oserratr/head-md-caran-ache-project/form/2023-12-11/forme2.pdf

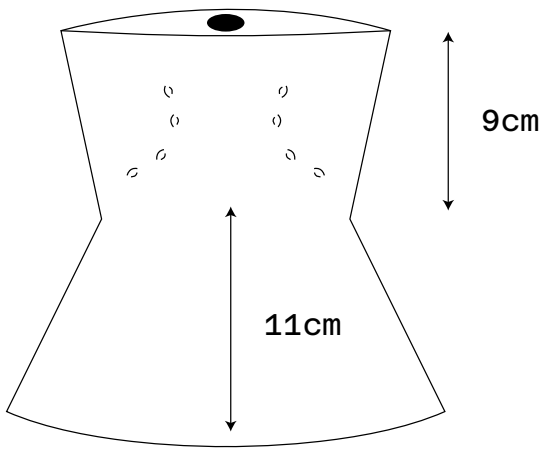
[picture p66: figure]
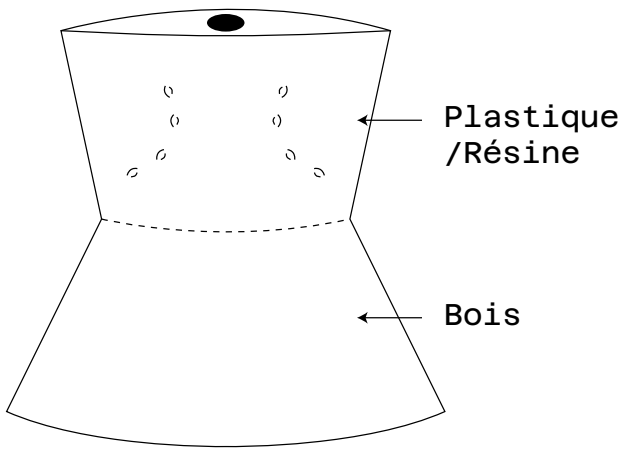
[picture p67: figure]
Bois; Plastique /Résine

20cm

Dimensions, matériaux, forme objet 2, prise a 2 mains

De côté

De dessus | 6cm

2cm

Bois peint
