oserratr/head-md-caran-ache-project/process/2023-11-13/part1-proto-final.pdf

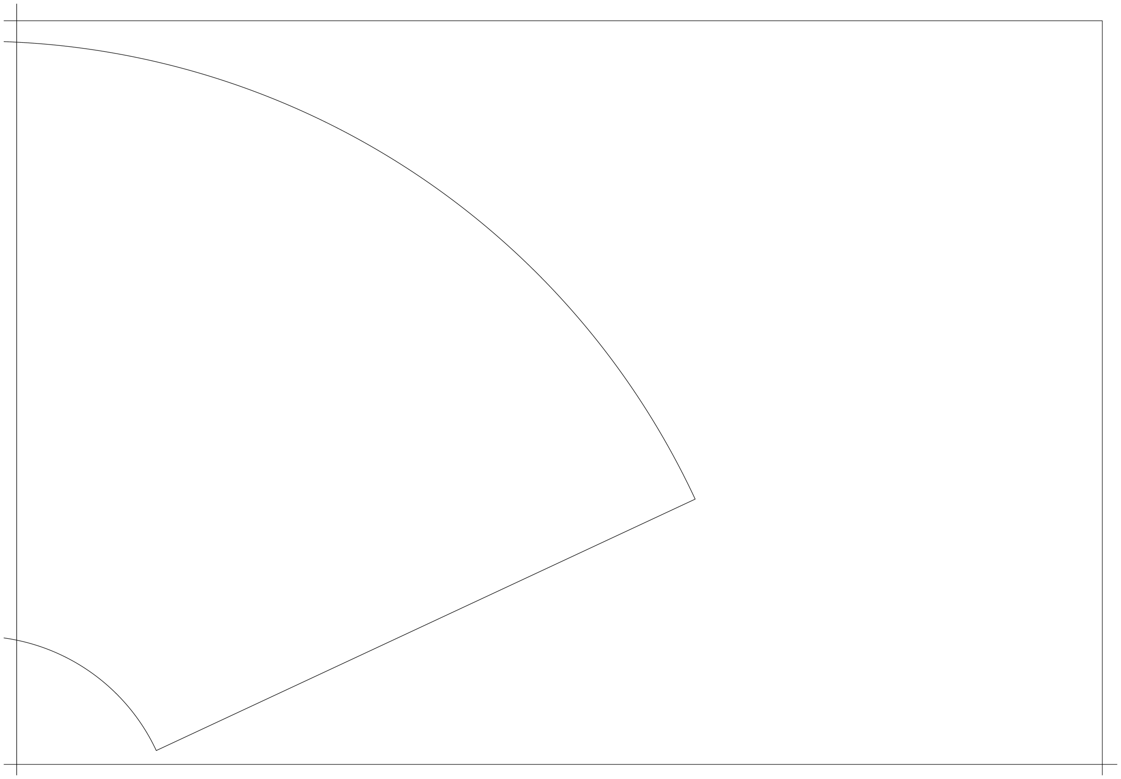
[picture p89: page 1]
