oserratr/head-md-caran-ache-project/process/2023-11-13/part2-proto-final.pdf

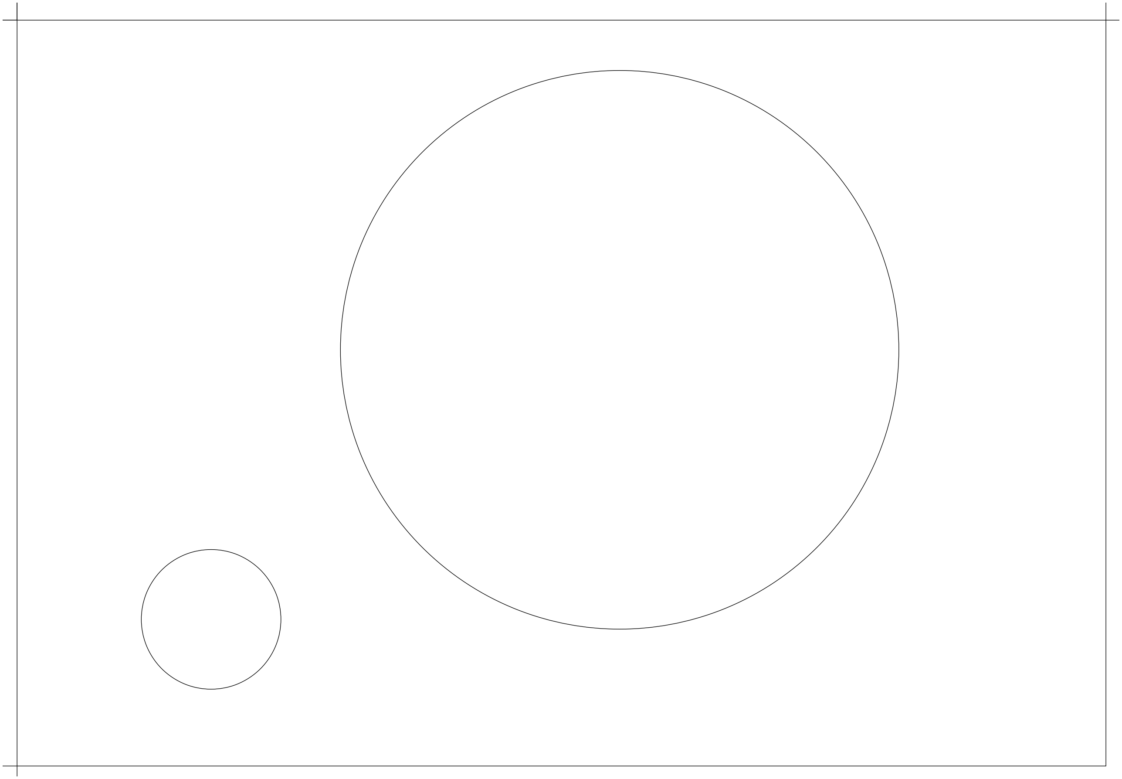
[picture p90: figure]
