oserratr/head-md-caran-ache-project/process/2023-11-13/part3-proto-final.pdf

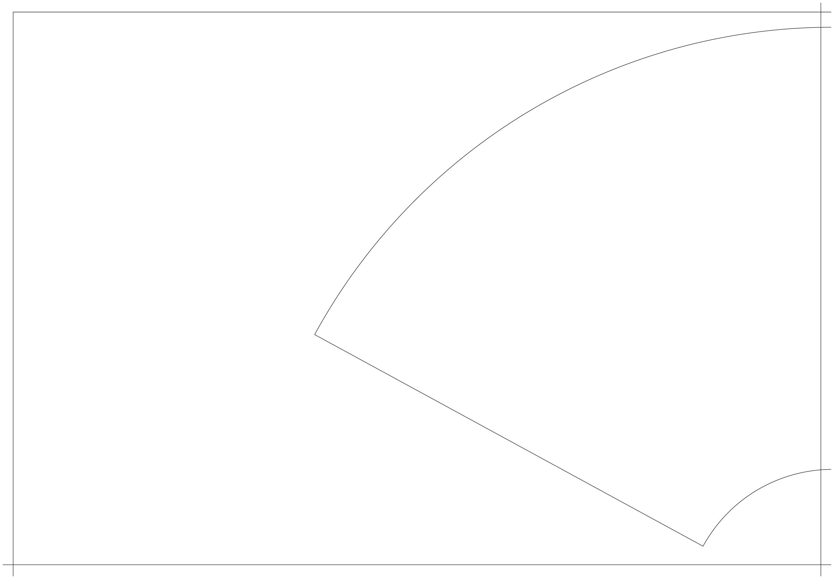
[picture p91: page 1]
