oserratr/head-md-caran-ache-project/process/2023-11-13/impression proto 2.pdf

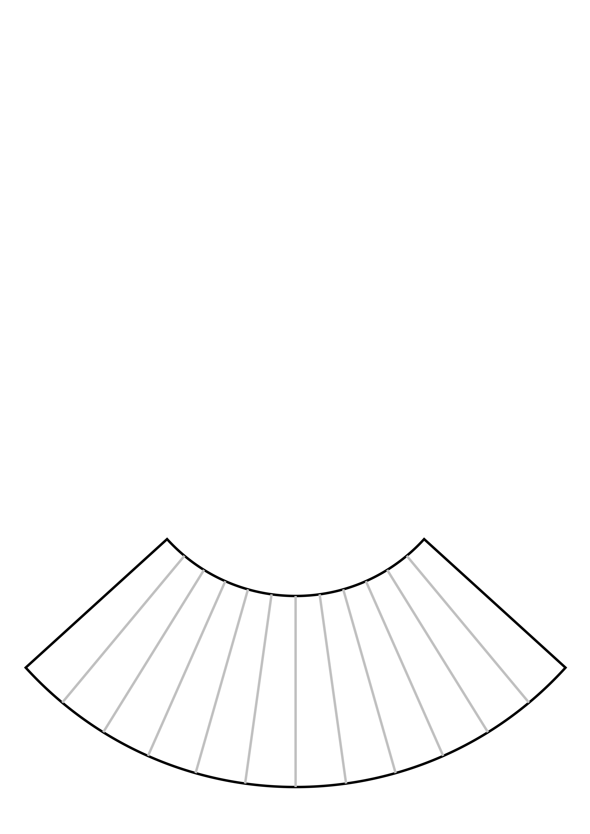
[picture p92: page 1]
