oserratr/head-md-caran-ache-project/process/2023-11-13/impression proto.pdf

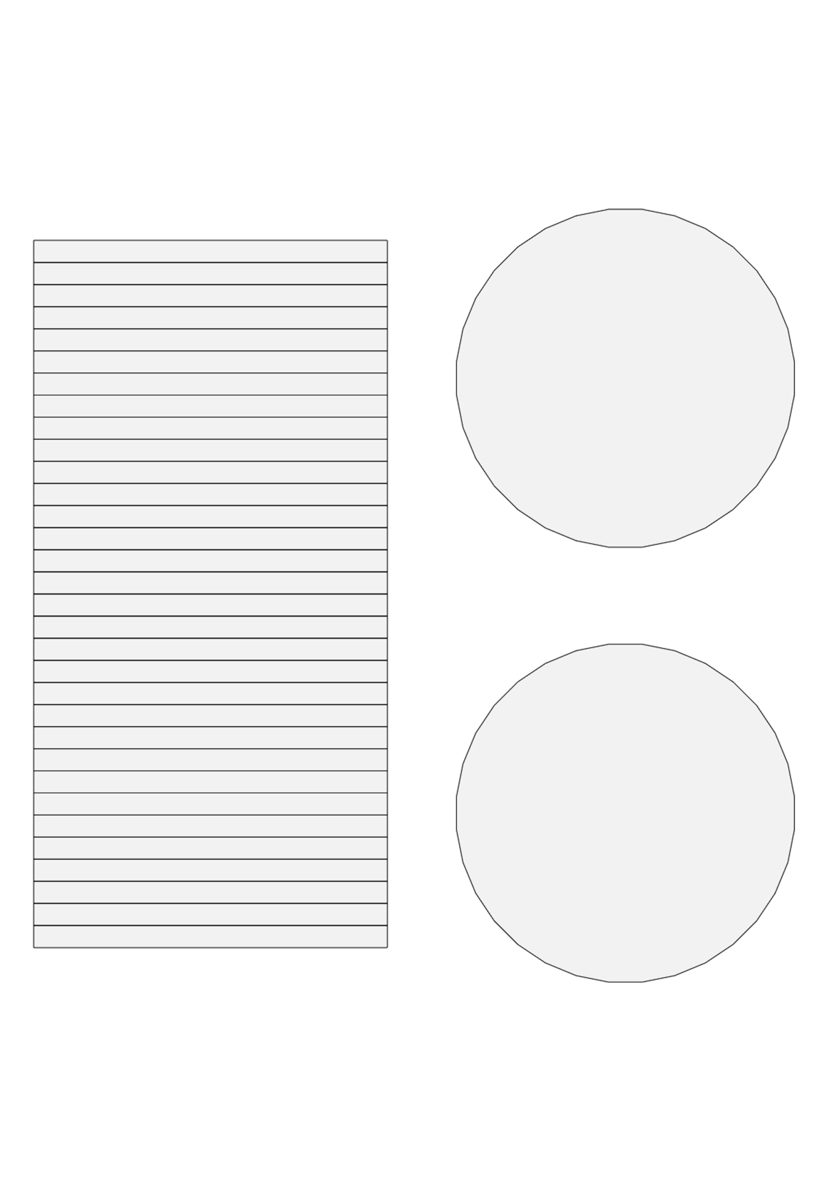
[picture p93: page 1]
