oserratr/head-md-caran-ache-project/electronics/2023-12-11/essais.png

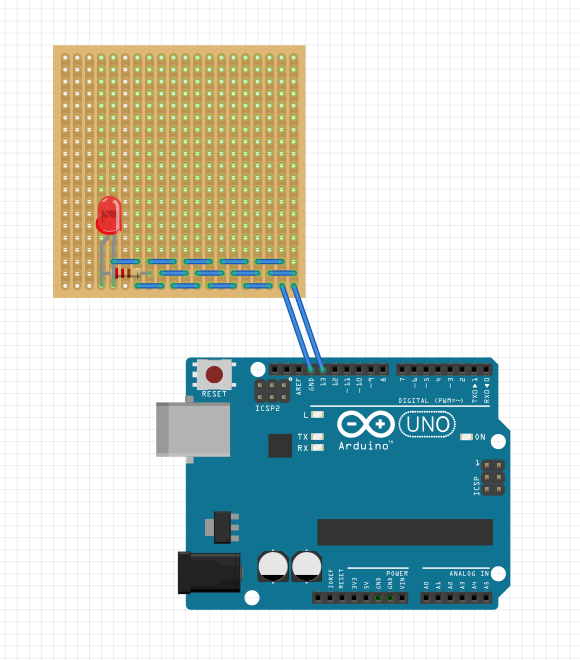
electronics/2023-12-11/essais.png
