oserratr/head-md-caran-ache-project/electronics/2023-12-11/shema.png

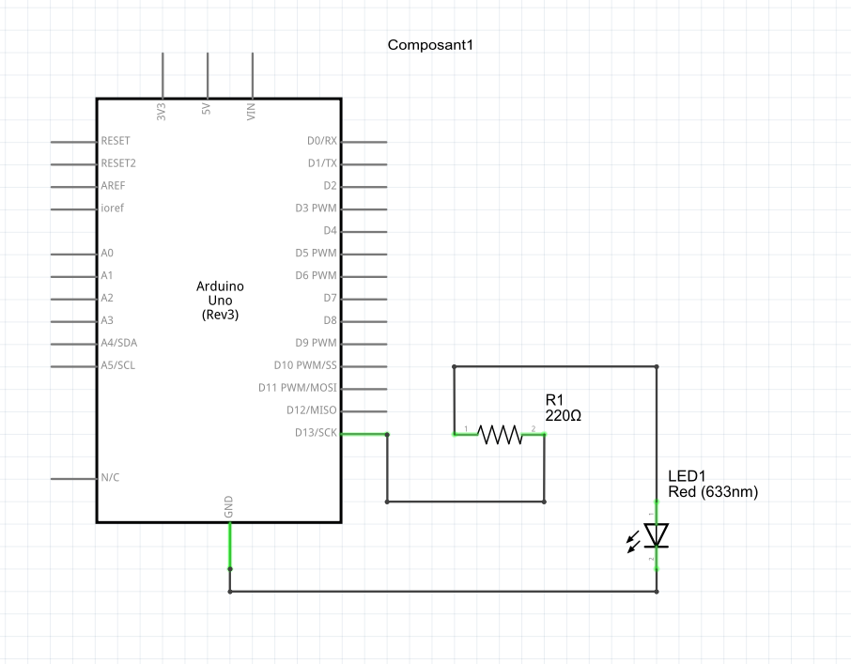
electronics/2023-12-11/shema.png
