oserratr/head-md-caran-ache-project/electronics/2023-12-21/connexion-bt-esp32-2.png

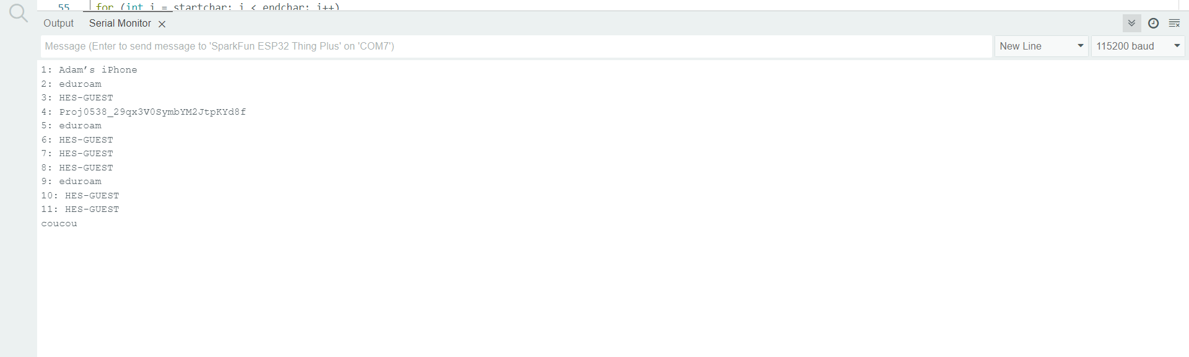
electronics/2023-12-21/connexion-bt-esp32-2.png
