oserratr/head-md-caran-ache-project/electronics/2024-01-14/landscape_design/output.png

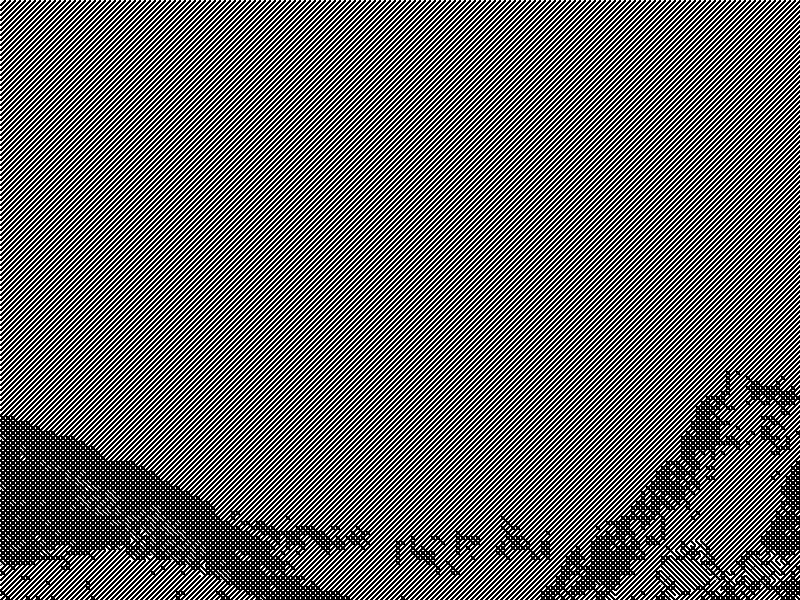
electronics/2024-01-14/landscape_design/output.png
