oserratr/head-md-caran-ache-project/form/2023-12-12/atelier1.jpg

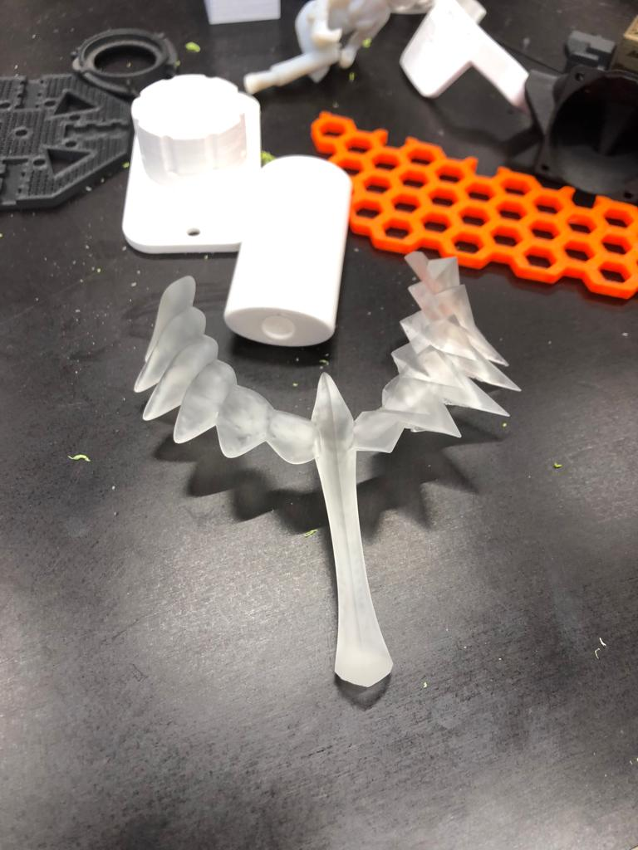
form/2023-12-12/atelier1.jpg
