oserratr/head-md-caran-ache-project/form/2023-12-12/dimensions-base-objet-bois.png

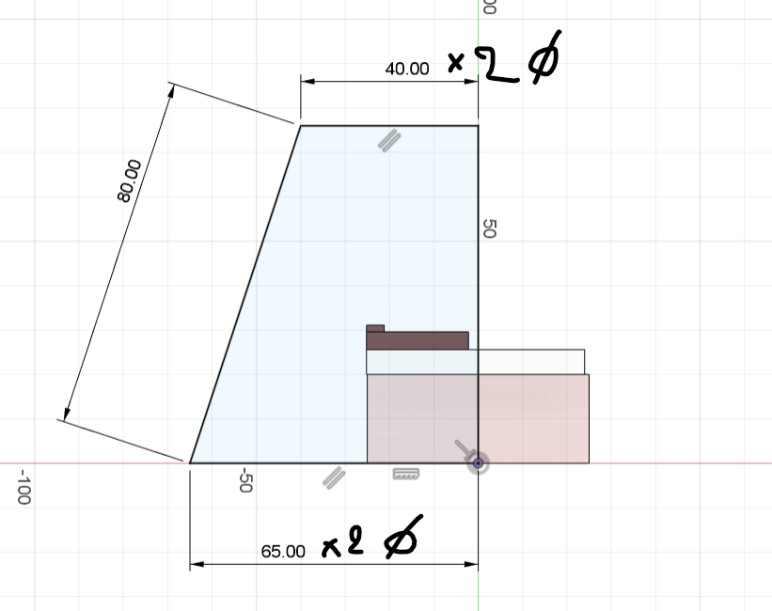
form/2023-12-12/dimensions-base-objet-bois.png
