oserratr/head-md-caran-ache-project/form/2023-12-12/dimensions-fixer-forme2.png

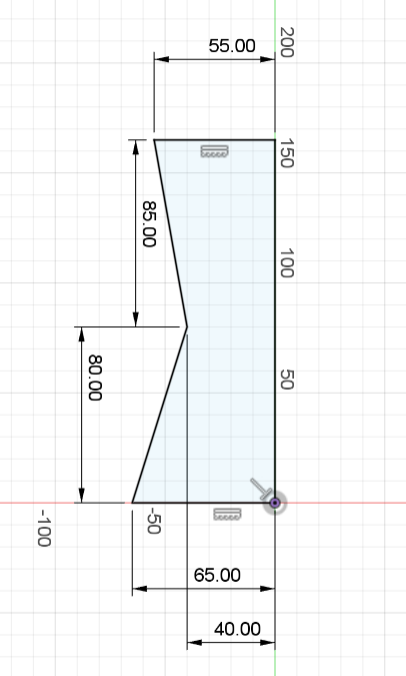
form/2023-12-12/dimensions-fixer-forme2.png
