oserratr/head-md-caran-ache-project/form/2023-12-12/taille-composants-inside.png

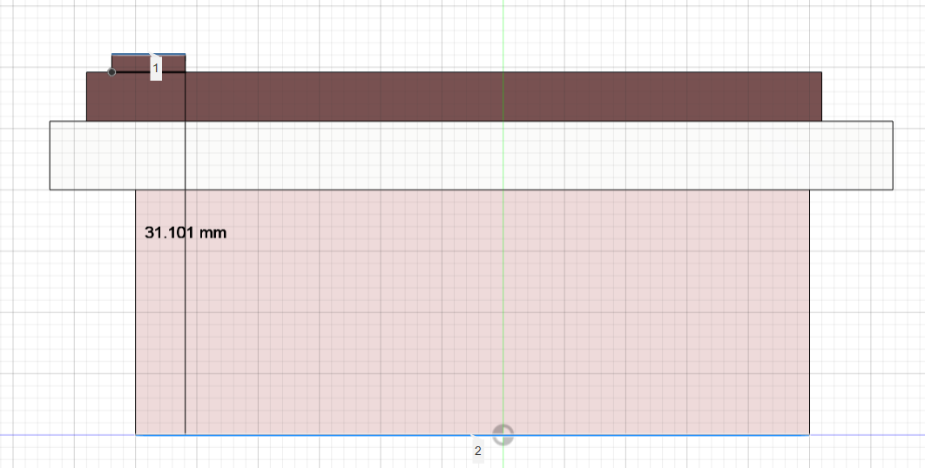
form/2023-12-12/taille-composants-inside.png
