oserratr/head-md-caran-ache-project/form/2023-12-19/manche.png

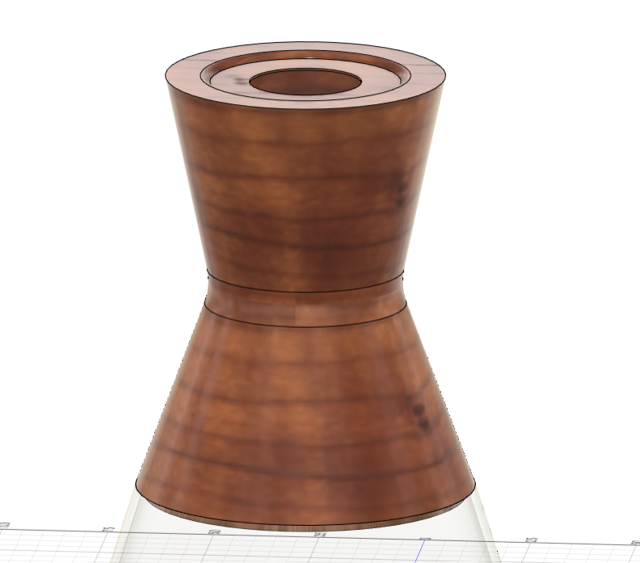
form/2023-12-19/manche.png
