oserratr/head-md-caran-ache-project/form/2023-12-19/socle.png

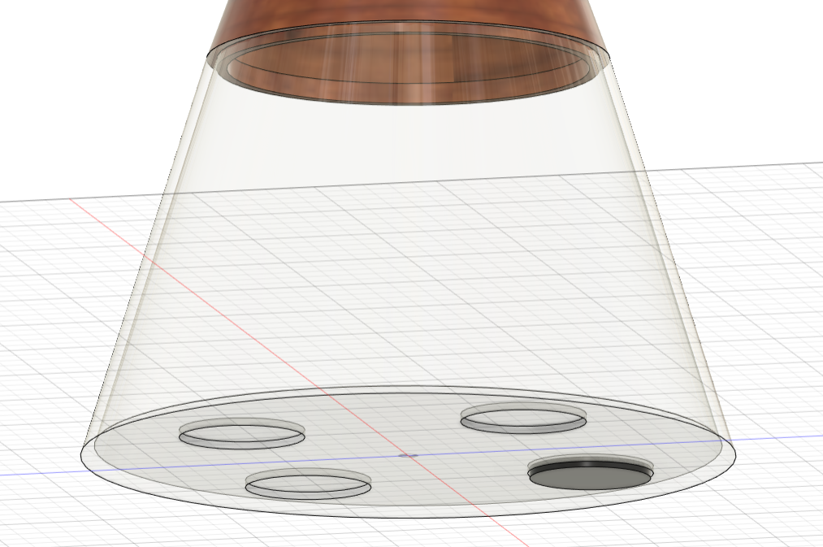
form/2023-12-19/socle.png
