oserratr/head-md-caran-ache-project/form/2023-12-20/impression manche.jpg

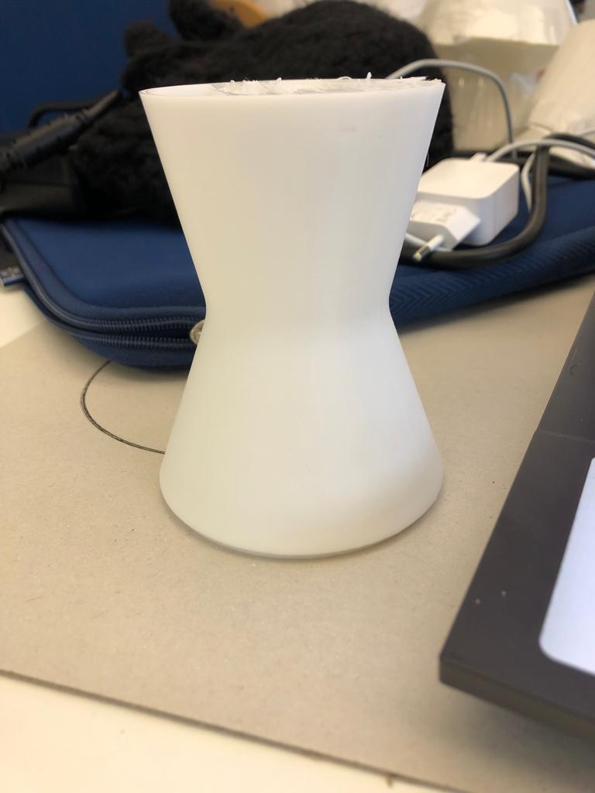
form/2023-12-20/impression manche.jpg
