oserratr/head-md-caran-ache-project/form/2023-12-20/materiel 3D2.jpg

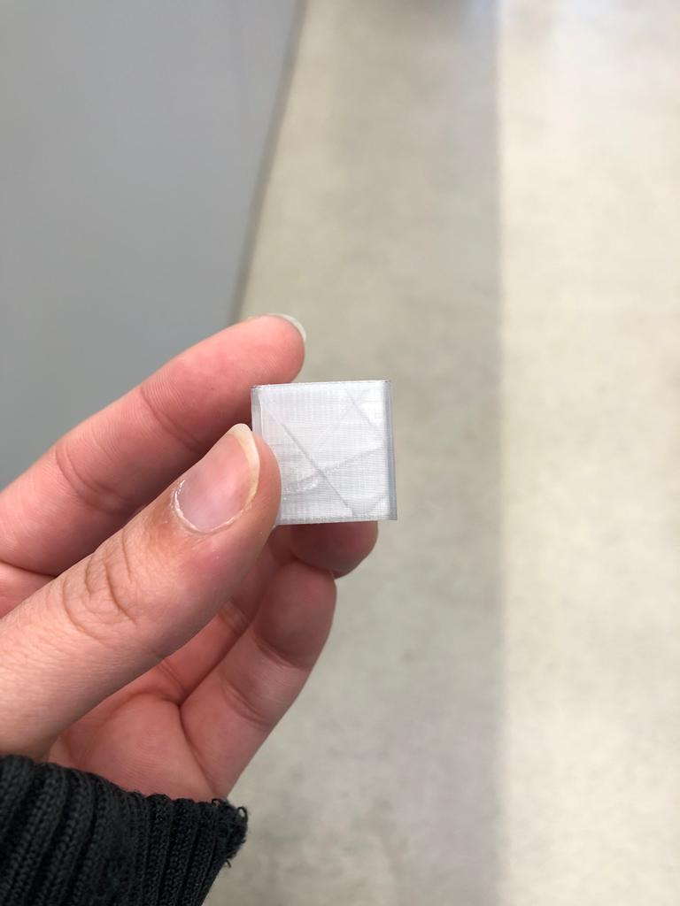
form/2023-12-20/materiel 3D2.jpg
