oserratr/head-md-caran-ache-project/form/2024-01-10/plan-drawing-input.jpg

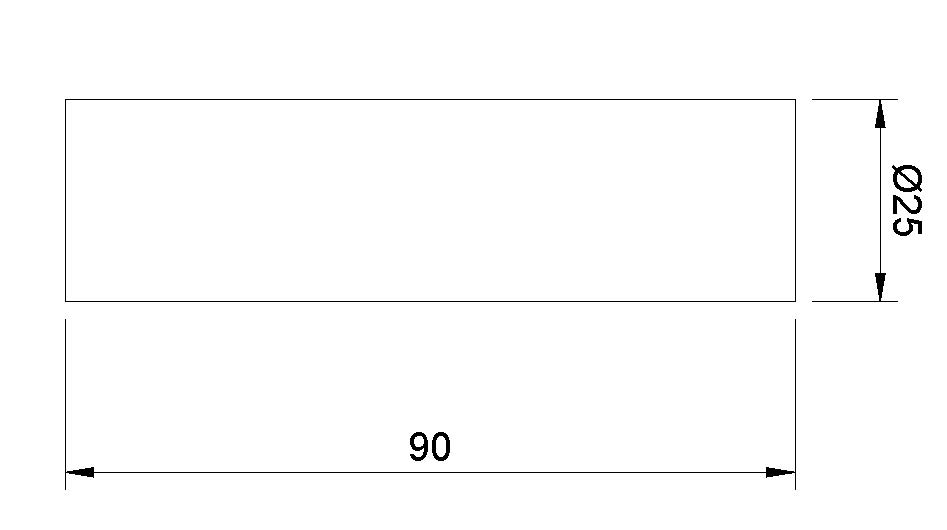
form/2024-01-10/plan-drawing-input.jpg
