oserratr/head-md-caran-ache-project/form/2024-01-10/plan-drawing-perspective.jpg

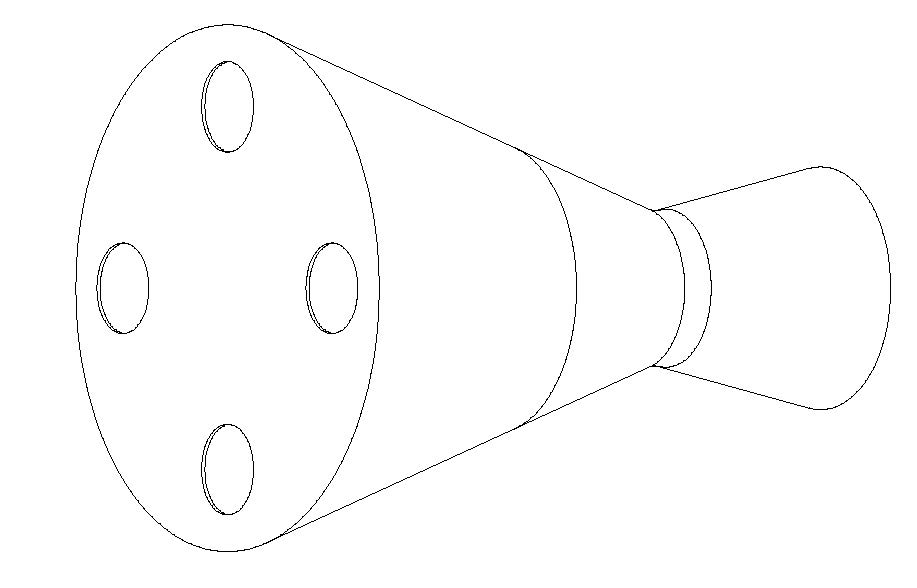
form/2024-01-10/plan-drawing-perspective.jpg
