oserratr/head-md-caran-ache-project/form/2024-01-10/plan-drawing-plateau-2.jpg

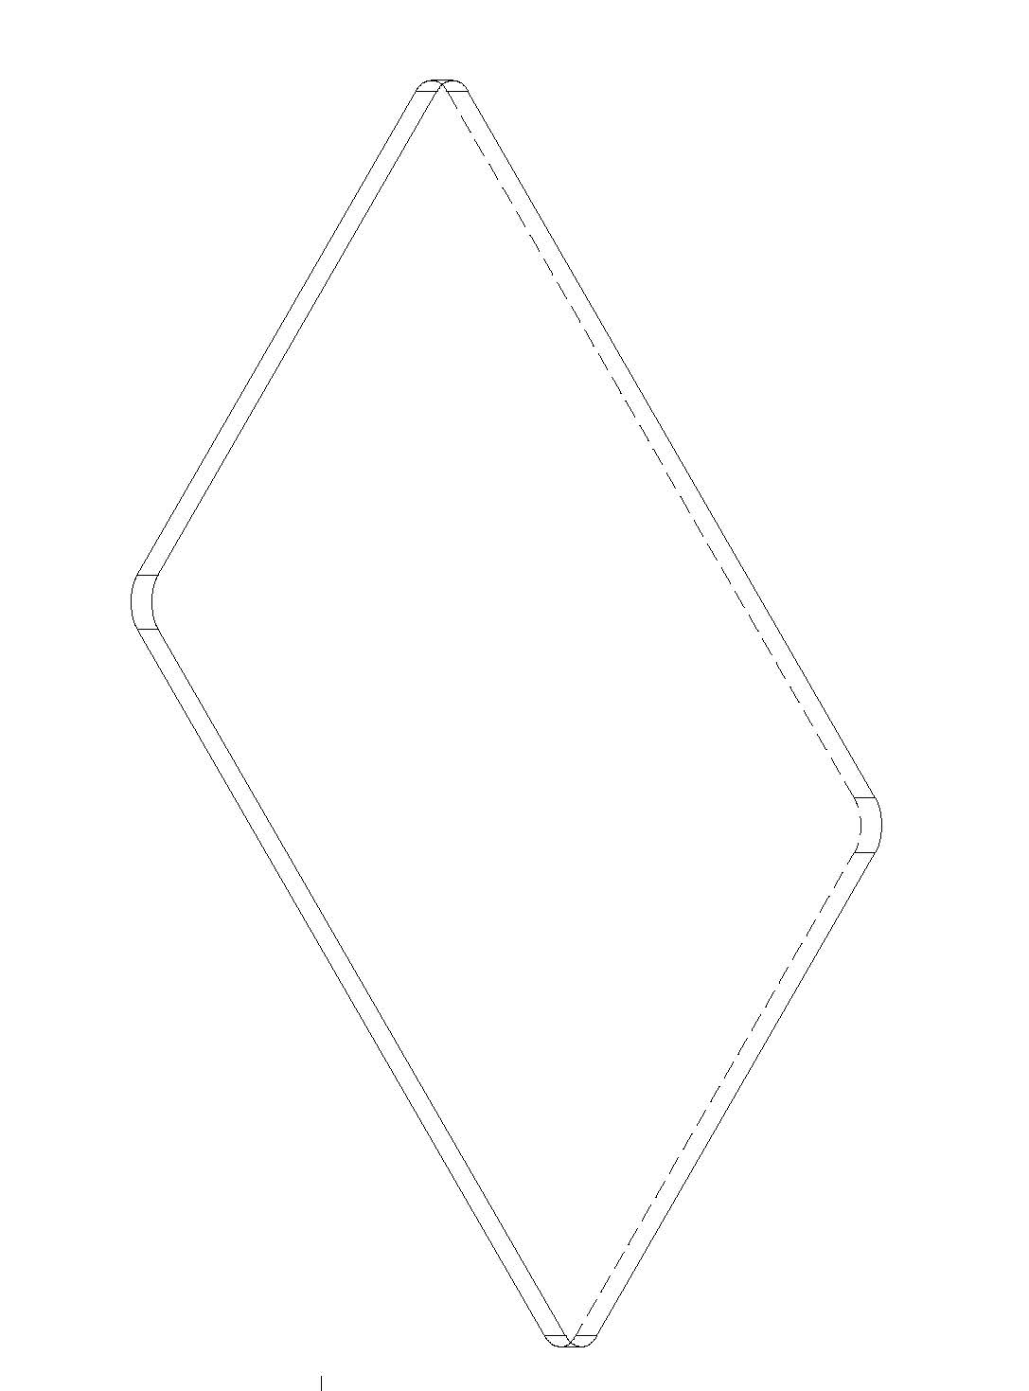
form/2024-01-10/plan-drawing-plateau-2.jpg
