oserratr/head-md-caran-ache-project/form/2024-01-10/plan-drawing-top.jpg

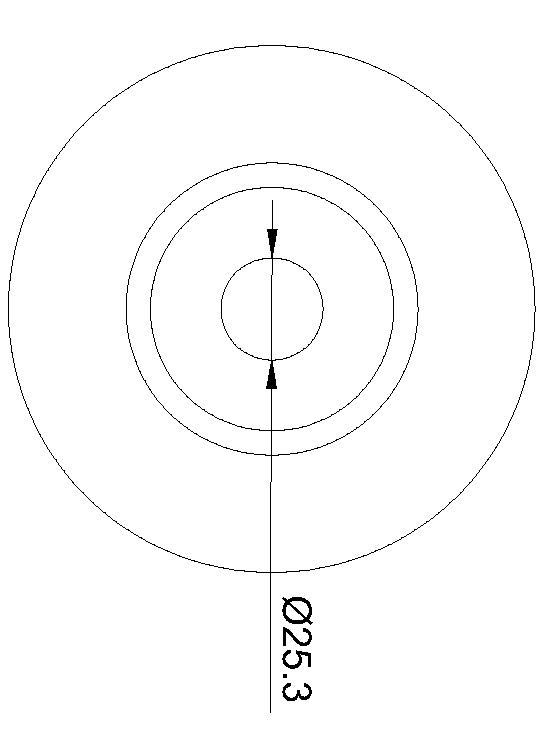
form/2024-01-10/plan-drawing-top.jpg
