oserratr/head-md-caran-ache-project/form/2024-01-11/rendu/rendu1-post.jpg

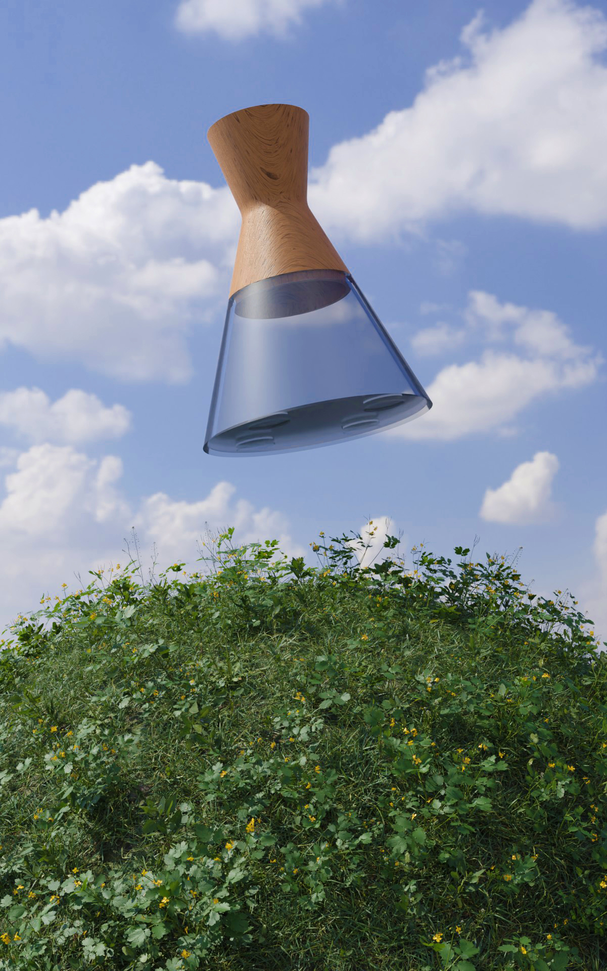
form/2024-01-11/rendu/rendu1-post.jpg
