oserratr/head-md-caran-ache-project/process/2023-10-25/proto-papier-cartes-1.jpeg

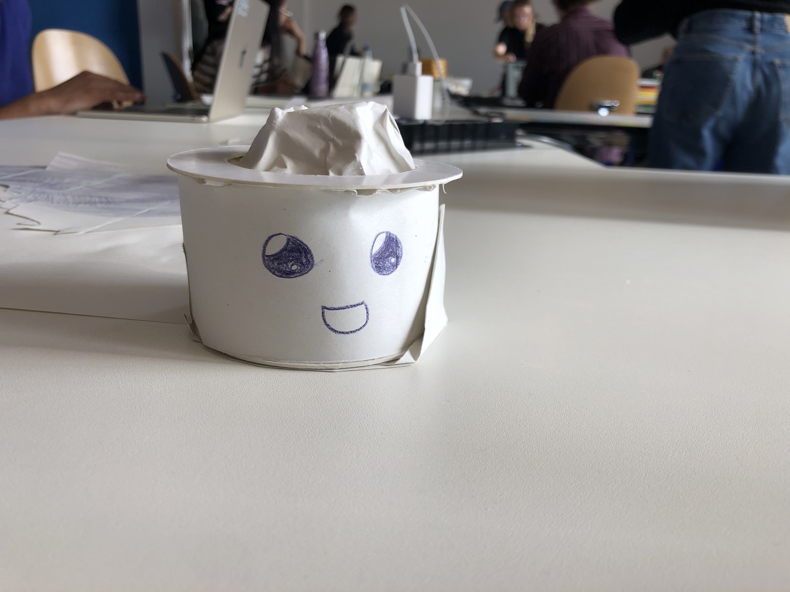
process/2023-10-25/proto-papier-cartes-1.jpeg
