oserratr/head-md-caran-ache-project/process/2023-10-25/proto-papier-cartes.jpeg

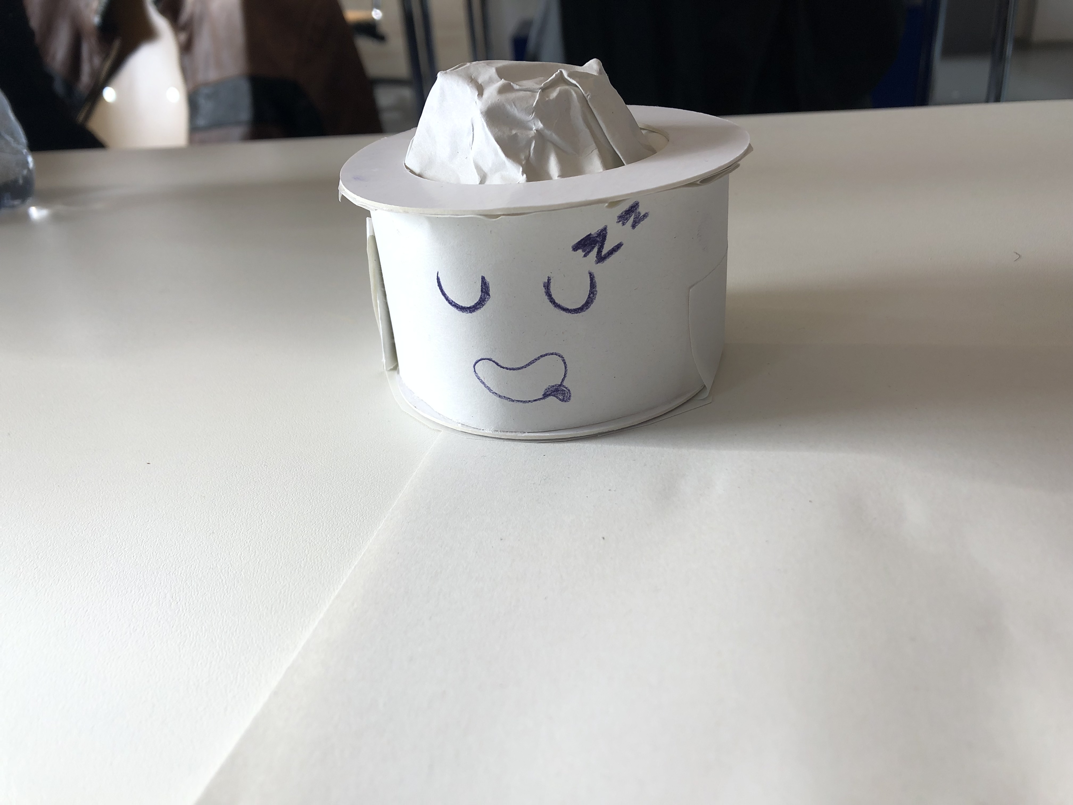
process/2023-10-25/proto-papier-cartes.jpeg
