oserratr/head-md-caran-ache-project/process/2023-10-25/schema-proto.jpg

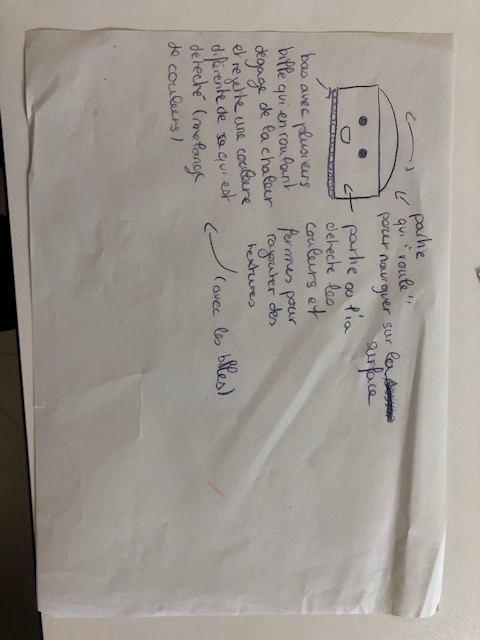
process/2023-10-25/schema-proto.jpg
