oserratr/head-md-caran-ache-project/process/2023-10-30/cote2.jpg

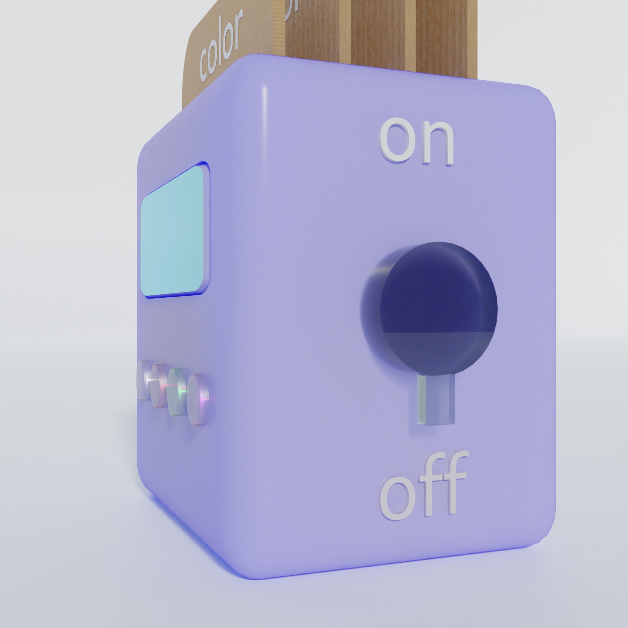
process/2023-10-30/cote2.jpg
