oserratr/head-md-caran-ache-project/process/2023-10-30/face.jpg

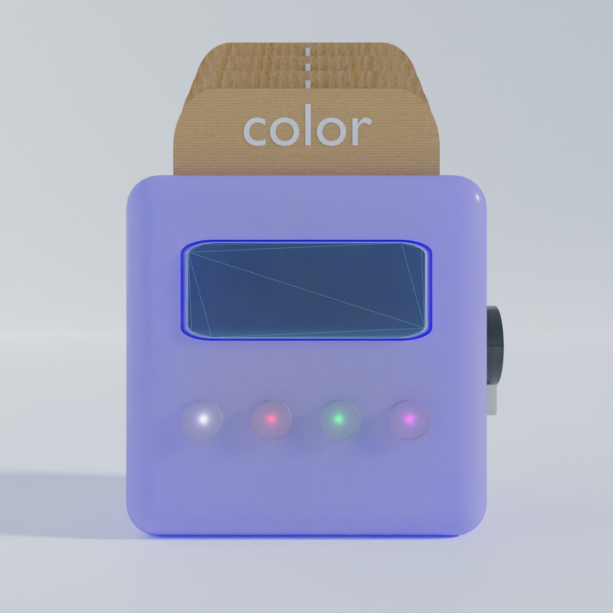
process/2023-10-30/face.jpg
