oserratr/head-md-caran-ache-project/process/2023-10-30/haut2.jpg

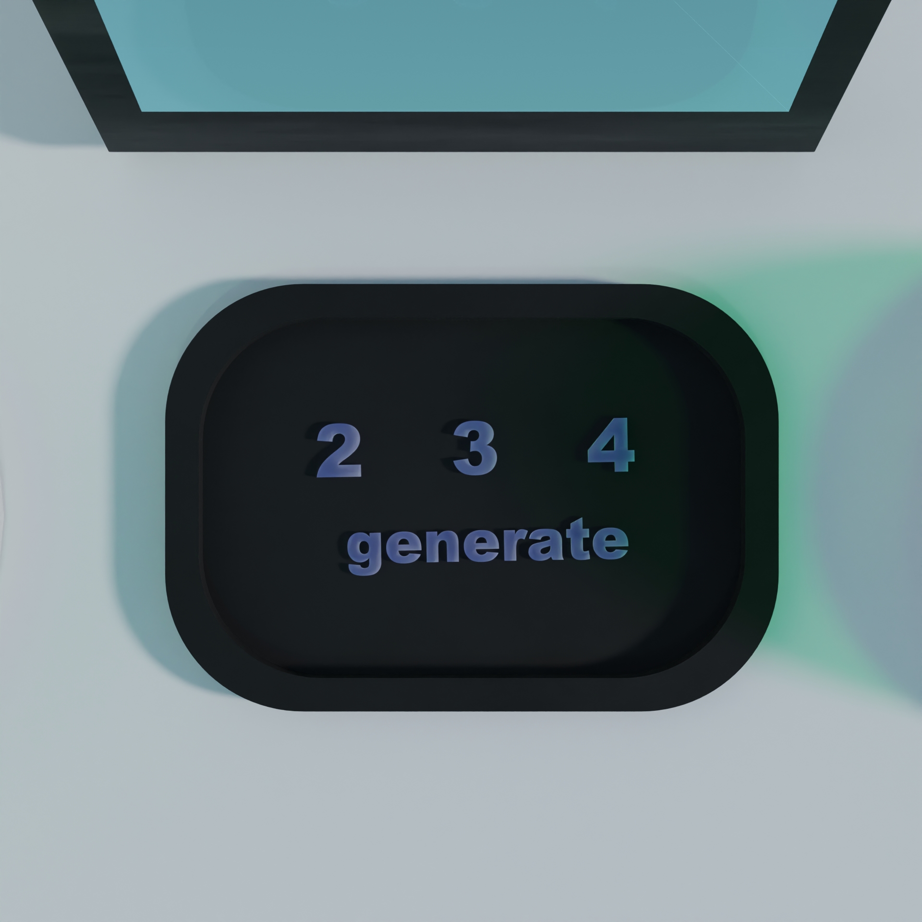
process/2023-10-30/haut2.jpg
