oserratr/head-md-caran-ache-project/process/2023-10-30/haut.jpg

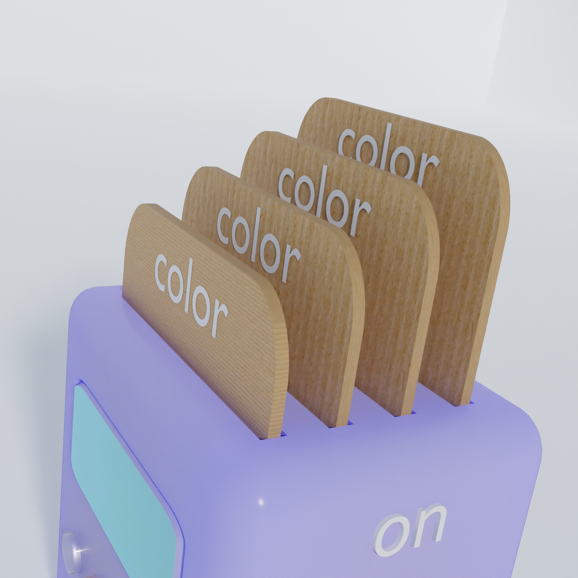
process/2023-10-30/haut.jpg
