oserratr/head-md-caran-ache-project/process/2023-10-30/proto-papier7.jpg

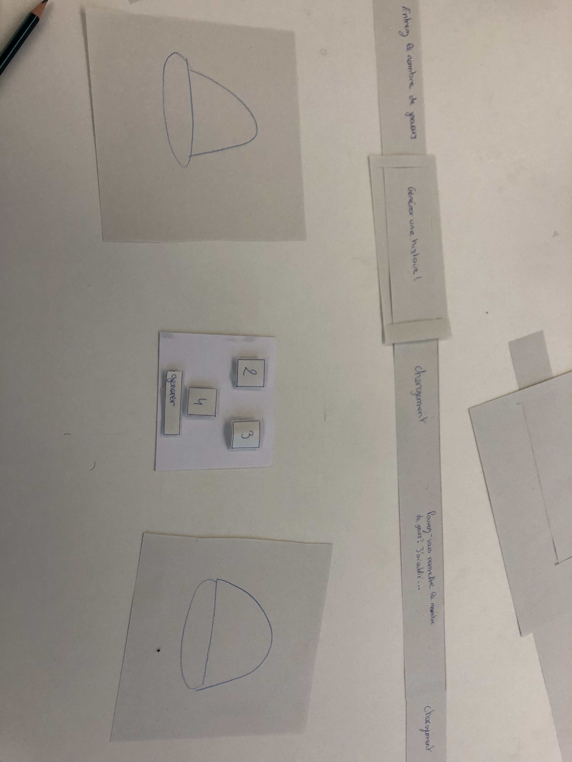
process/2023-10-30/proto-papier7.jpg
