oserratr/head-md-caran-ache-project/process/2023-11-07/arbre-ar.png

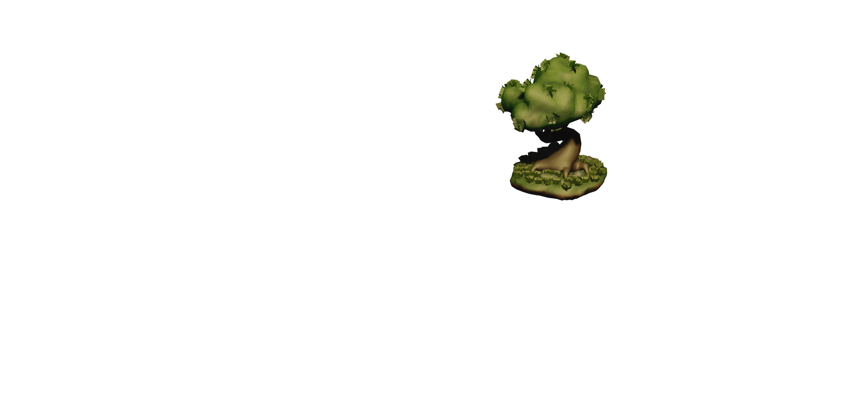
process/2023-11-07/arbre-ar.png
