oserratr/head-md-caran-ache-project/process/2023-11-07/Isolated_right_hand_with_smartphone.png

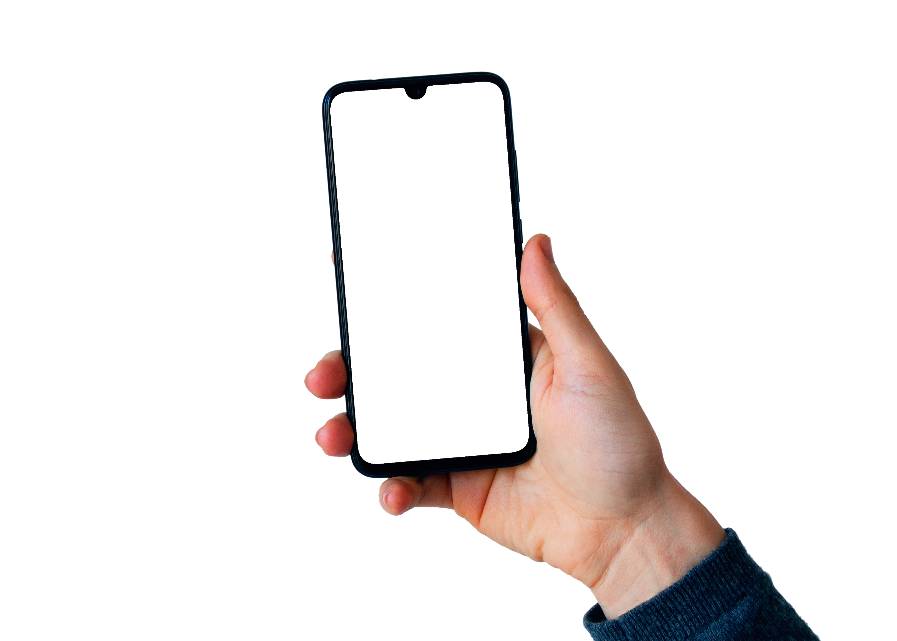
process/2023-11-07/Isolated_right_hand_with_smartphone.png
