oserratr/head-md-caran-ache-project/process/2023-11-07/plateau-interactif.png

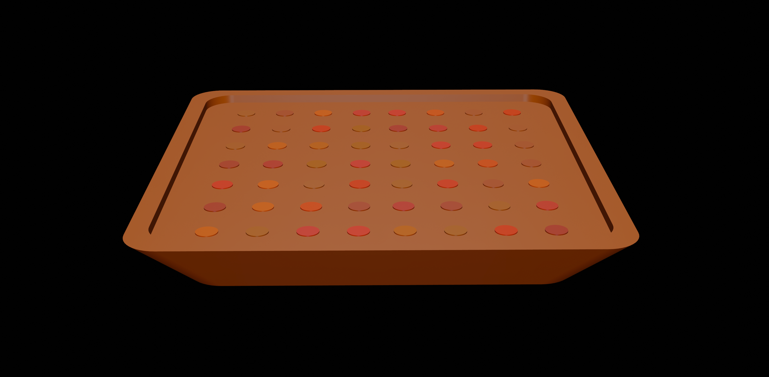
process/2023-11-07/plateau-interactif.png
