oserratr/head-md-caran-ache-project/process/2023-11-08/boite transp.png

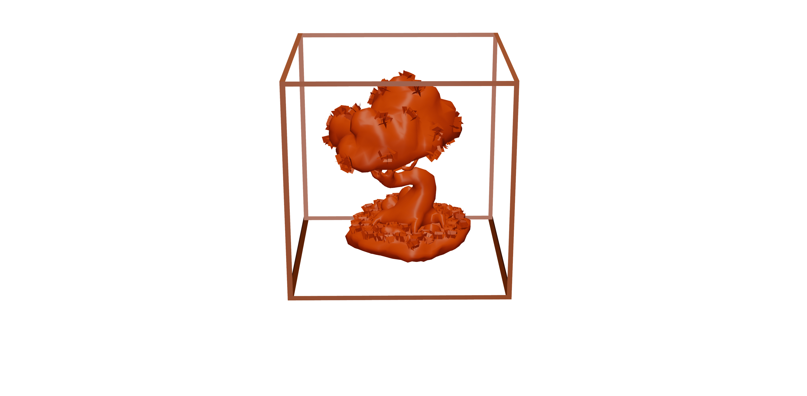
process/2023-11-08/boite transp.png
