oserratr/head-md-caran-ache-project/process/2023-11-08/crayon sans assm.png

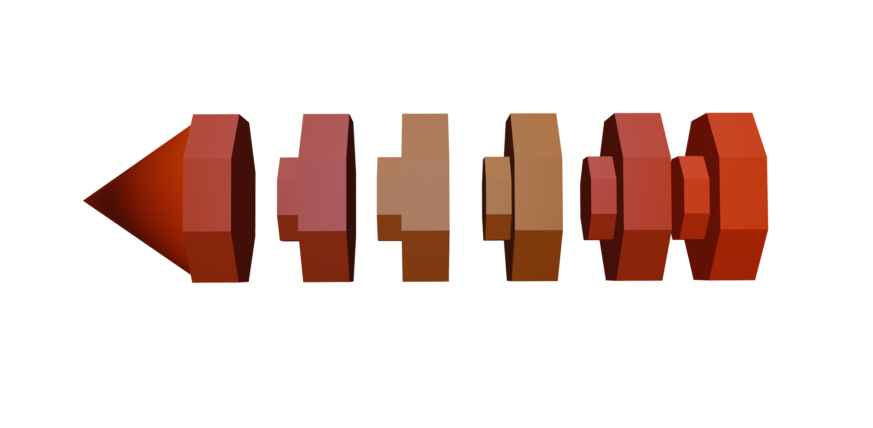
process/2023-11-08/crayon sans assm.png
