oserratr/head-md-caran-ache-project/process/2023-11-12/etape100.png

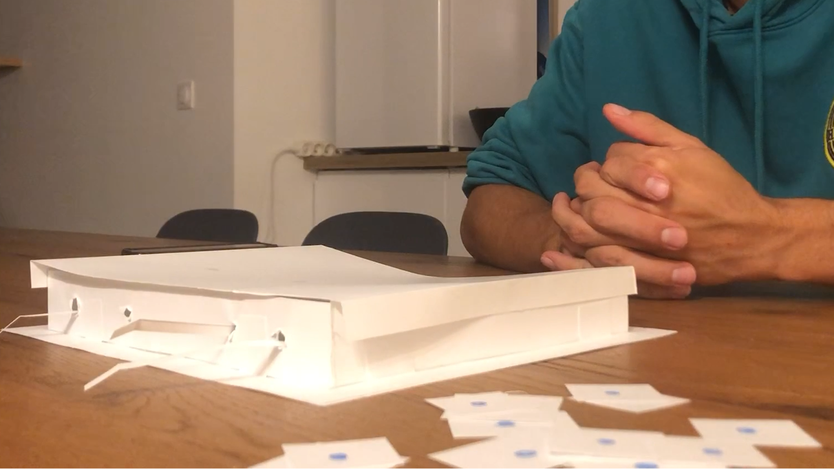
process/2023-11-12/etape100.png
