oserratr/head-md-caran-ache-project/process/2023-11-12/IMG_32150.png

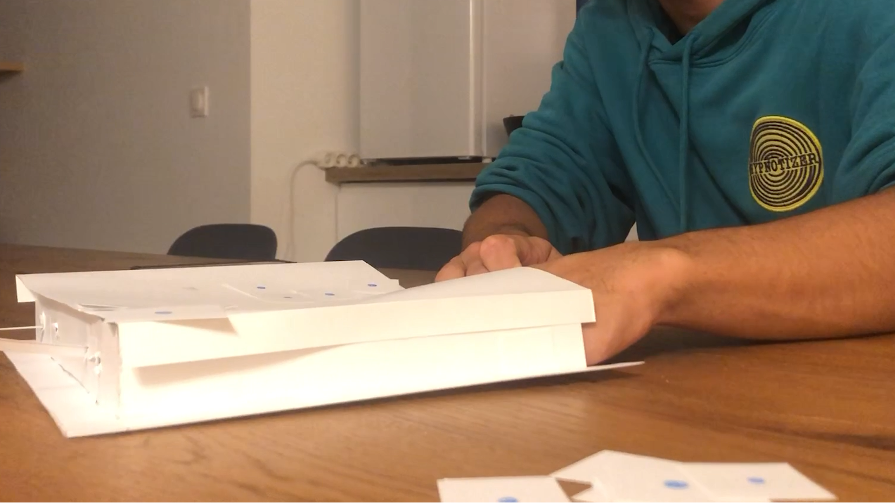
process/2023-11-12/IMG_32150.png
