oserratr/head-md-caran-ache-project/process/2023-11-12/IMG_32160.png

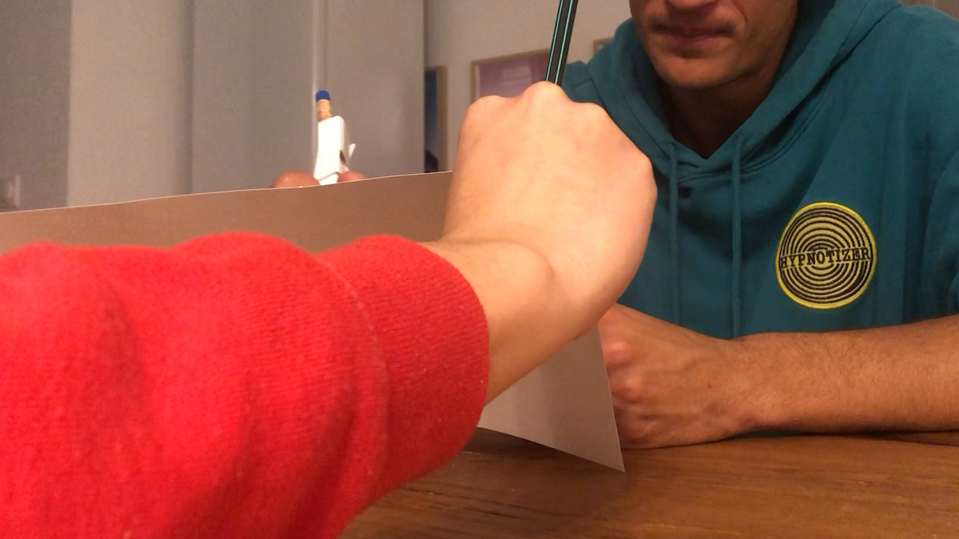
process/2023-11-12/IMG_32160.png
