oserratr/head-md-caran-ache-project/process/2023-11-12/IMG_321517.png

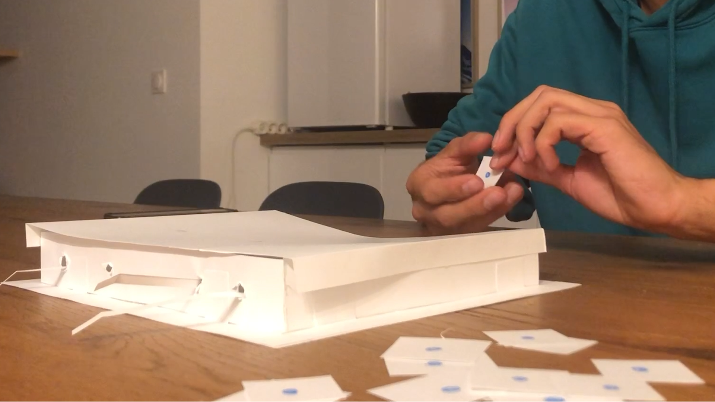
process/2023-11-12/IMG_321517.png
