oserratr/head-md-caran-ache-project/process/2023-11-12/prot20.png

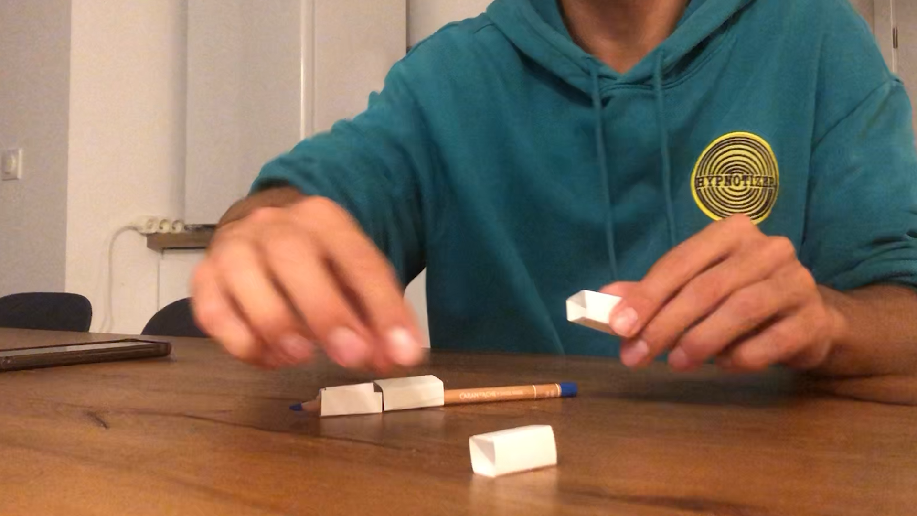
process/2023-11-12/prot20.png
