oserratr/head-md-caran-ache-project/process/2023-11-13/proto-wrap-1.png

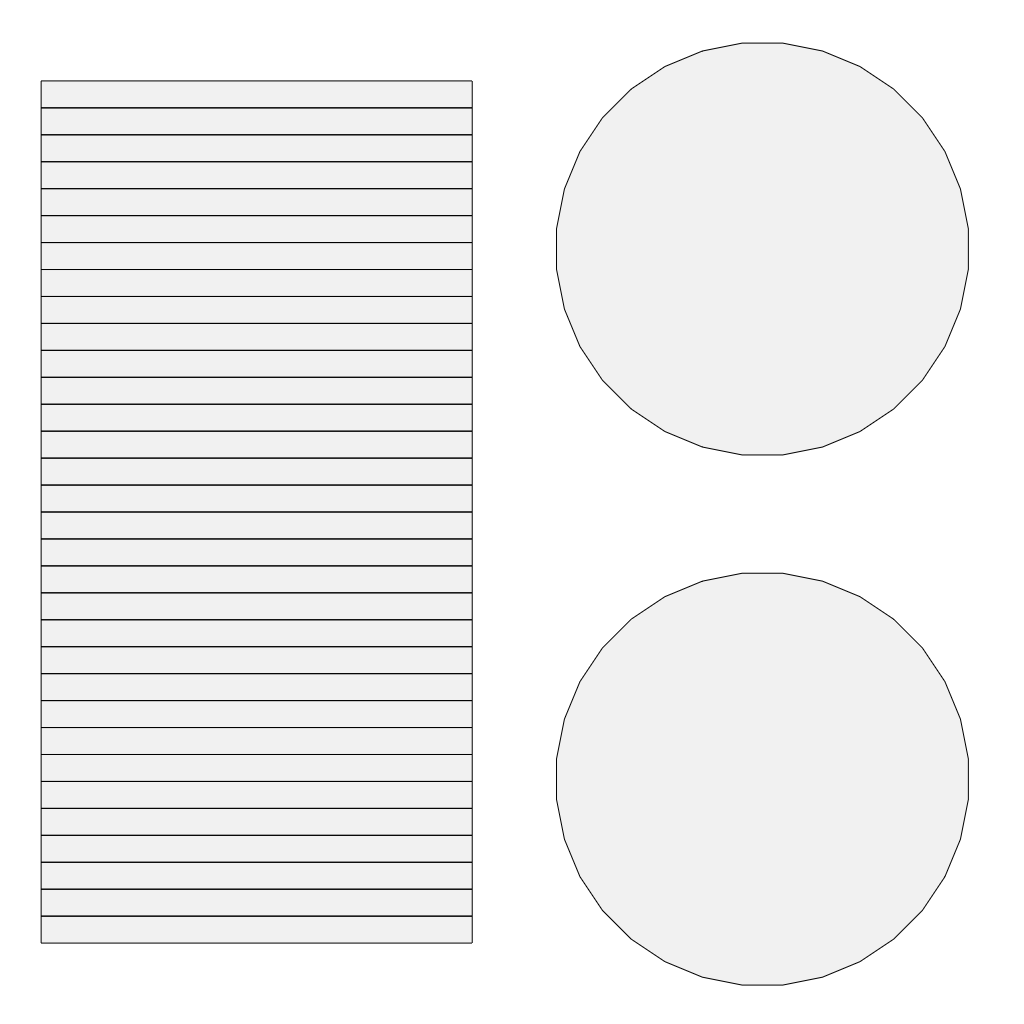
process/2023-11-13/proto-wrap-1.png
