oserratr/head-md-caran-ache-project/process/2023-11-13/user journey_User journey prototype 2.jpg

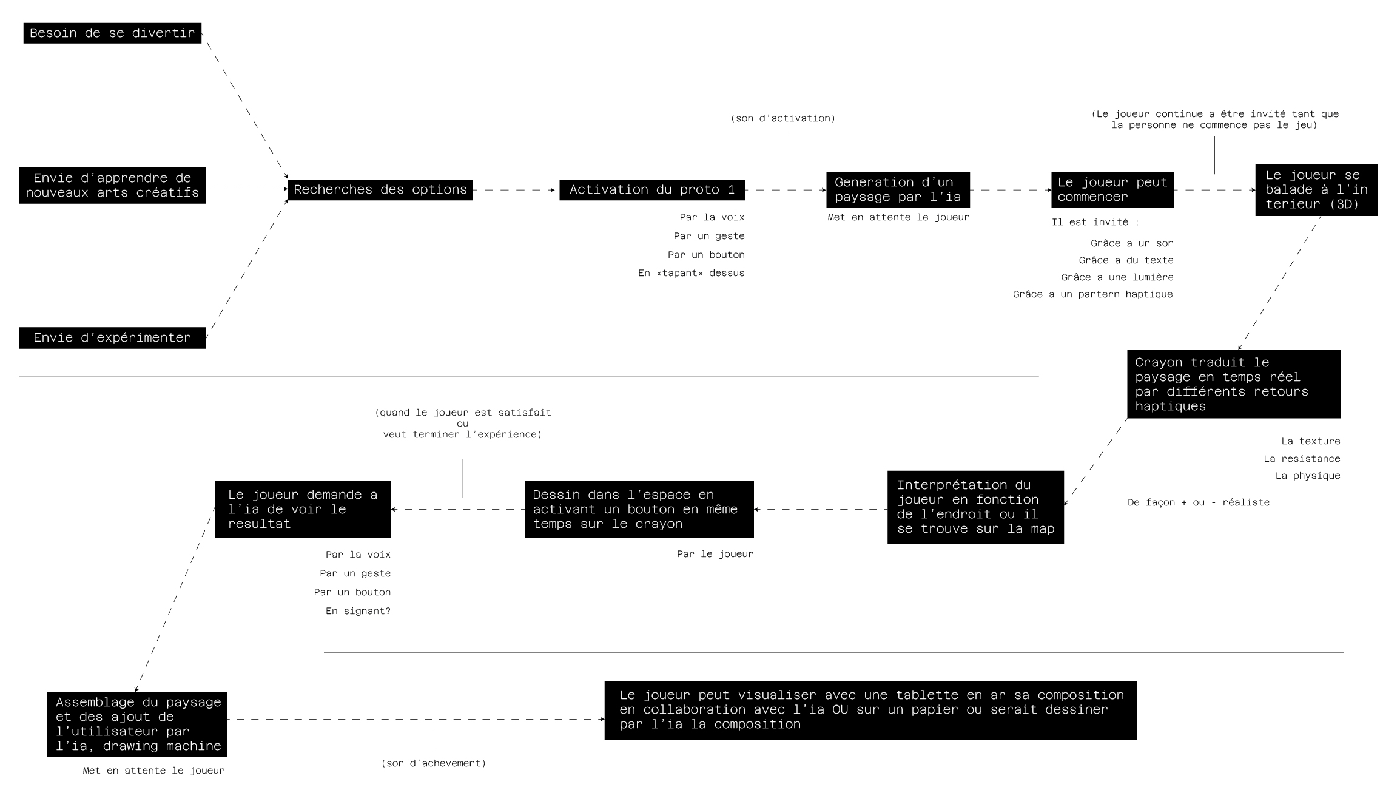
process/2023-11-13/user journey_User journey prototype 2.jpg
