oserratr/head-md-caran-ache-project/process/2023-11-14/B98130A4-3346-42A7-AB67-82BB6E55FD4F.jpeg

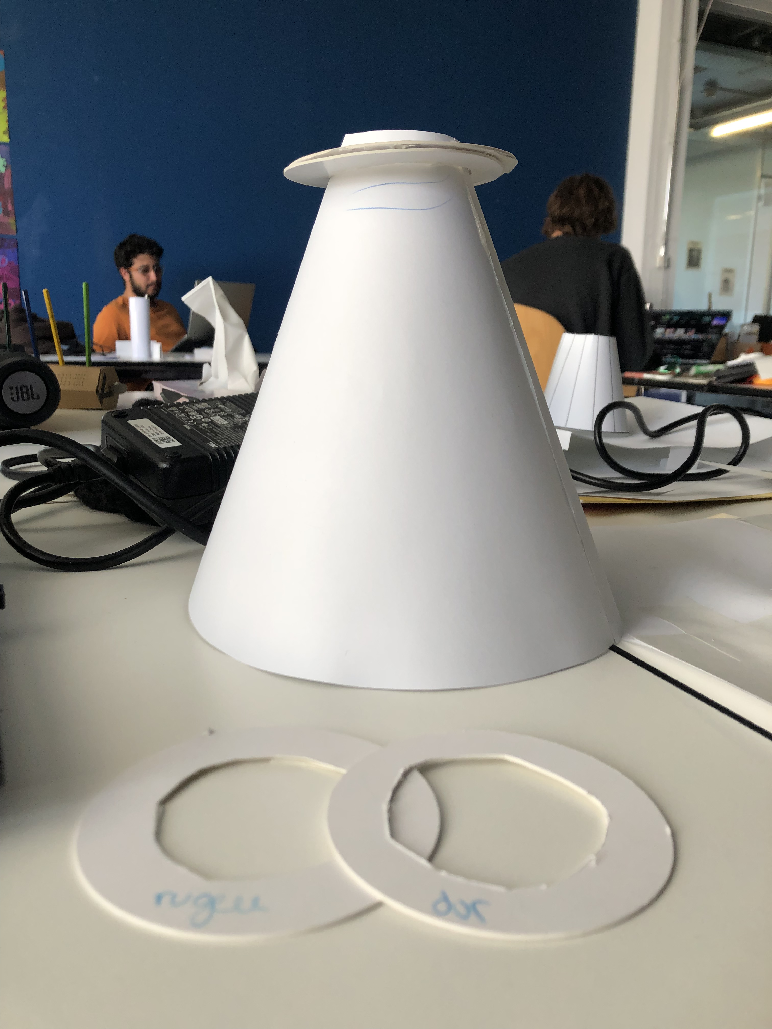
process/2023-11-14/B98130A4-3346-42A7-AB67-82BB6E55FD4F.jpeg
