oserratr/head-md-caran-ache-project/process/2023-11-14/F321C655-03D5-4F41-8056-327A12E2EA54.jpeg

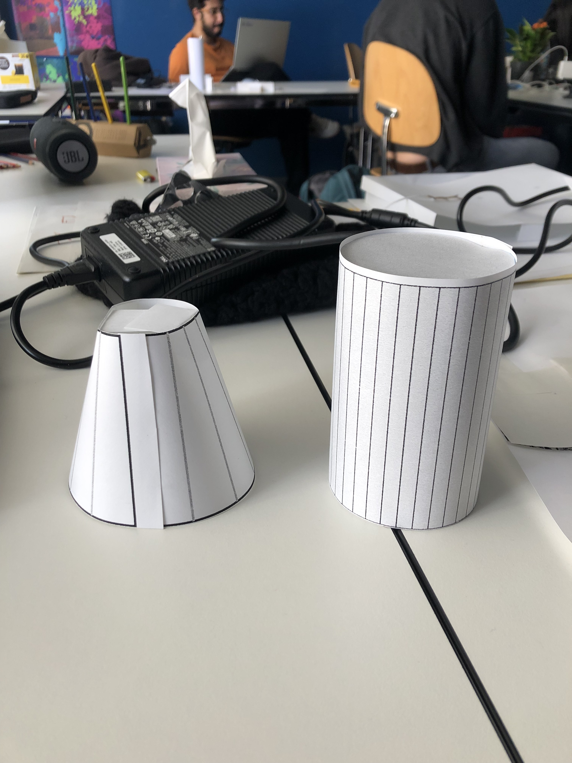
process/2023-11-14/F321C655-03D5-4F41-8056-327A12E2EA54.jpeg
