oserratr/head-md-caran-ache-project/process/2023-11-15/1.jpg

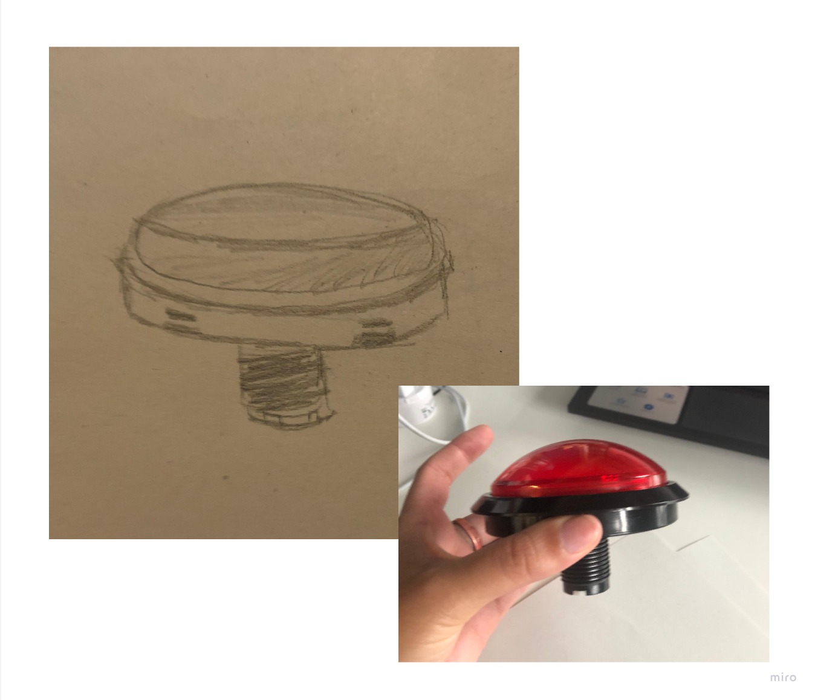
process/2023-11-15/1.jpg
