oserratr/head-md-caran-ache-project/process/2023-11-15/2.jpg

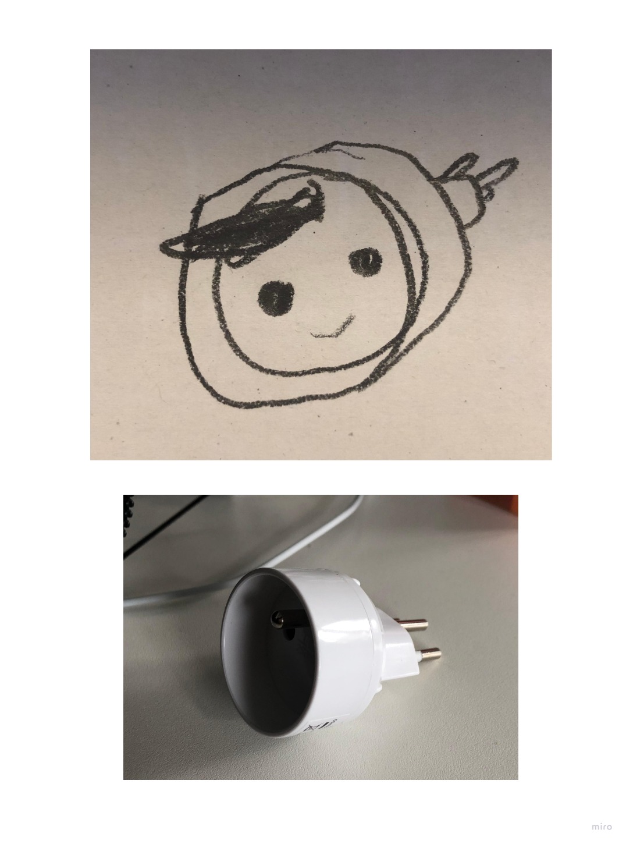
process/2023-11-15/2.jpg
