oserratr/head-md-caran-ache-project/process/2023-11-15/2ED60508-EEB2-4C9A-83B8-20BE05BEABDE.jpeg

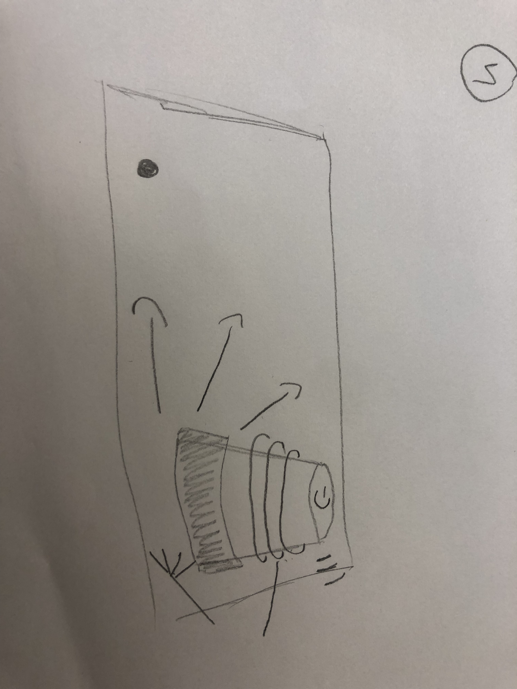
process/2023-11-15/2ED60508-EEB2-4C9A-83B8-20BE05BEABDE.jpeg
