oserratr/head-md-caran-ache-project/process/2023-11-15/9C8A12C2-044F-475F-8F20-B294329259E3.jpeg

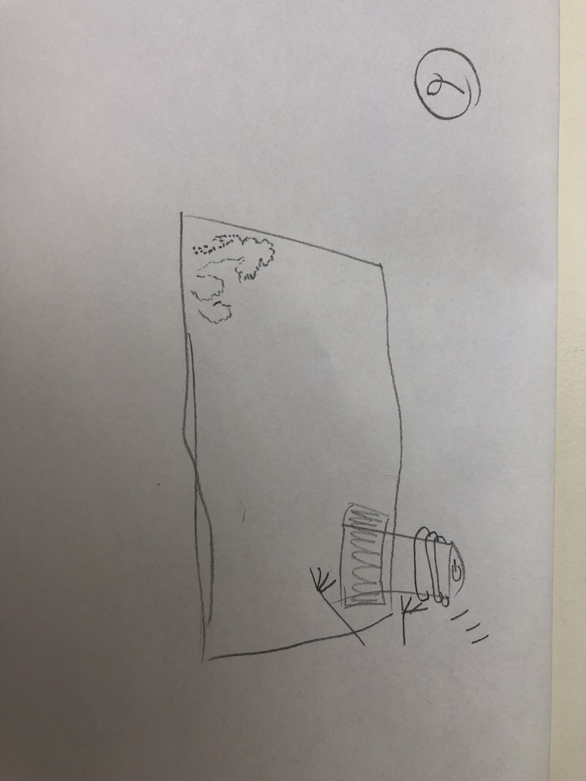
process/2023-11-15/9C8A12C2-044F-475F-8F20-B294329259E3.jpeg
