oserratr/head-md-caran-ache-project/process/2023-11-15/12CF48D4-84FD-4676-80A5-F36BA82219FC.jpeg

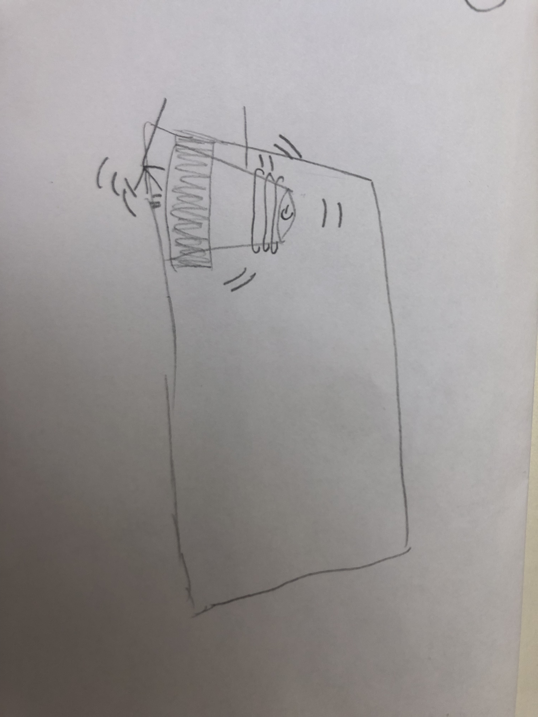
process/2023-11-15/12CF48D4-84FD-4676-80A5-F36BA82219FC.jpeg
