oserratr/head-md-caran-ache-project/process/2023-11-15/17CA061B-6AFC-4FA0-AF5B-634BB94ADFA1.jpeg

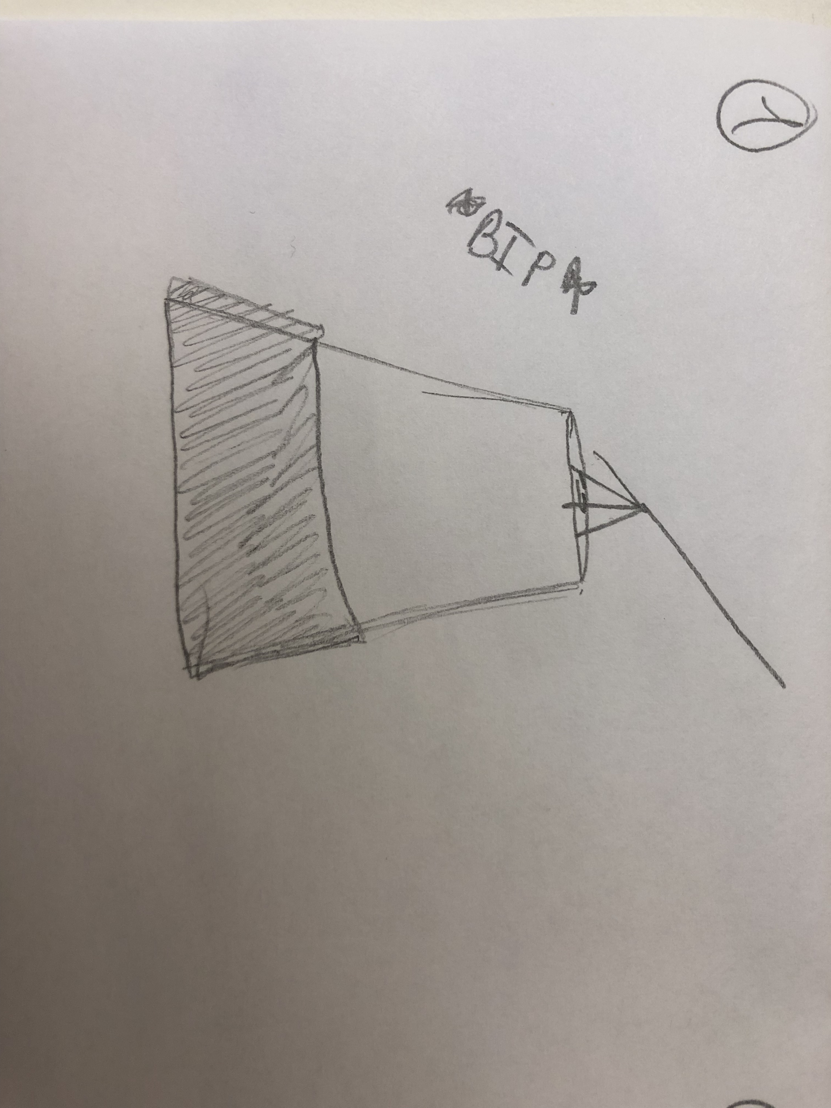
process/2023-11-15/17CA061B-6AFC-4FA0-AF5B-634BB94ADFA1.jpeg
