oserratr/head-md-caran-ache-project/process/2023-11-15/A5C848FB-1FE0-404E-A0E0-270594D7527A.jpeg

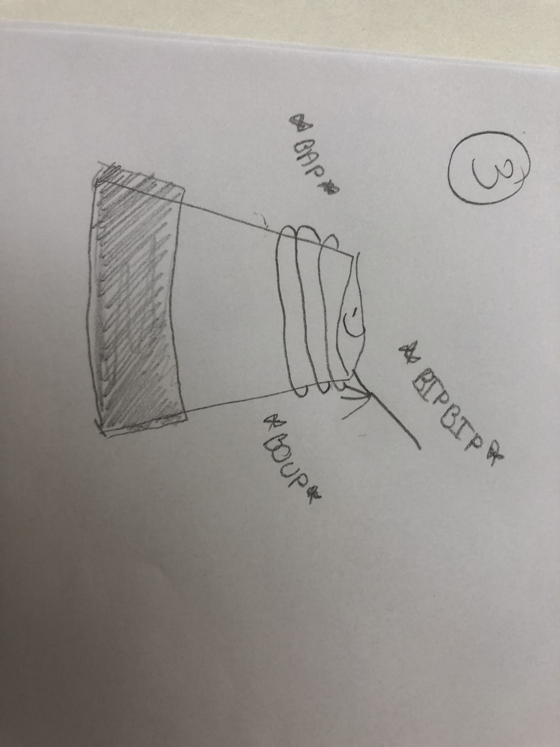
process/2023-11-15/A5C848FB-1FE0-404E-A0E0-270594D7527A.jpeg
