oserratr/head-md-caran-ache-project/process/2023-11-15/F52EEC8F-537B-4D7C-88F3-462B25EA2E29.jpeg

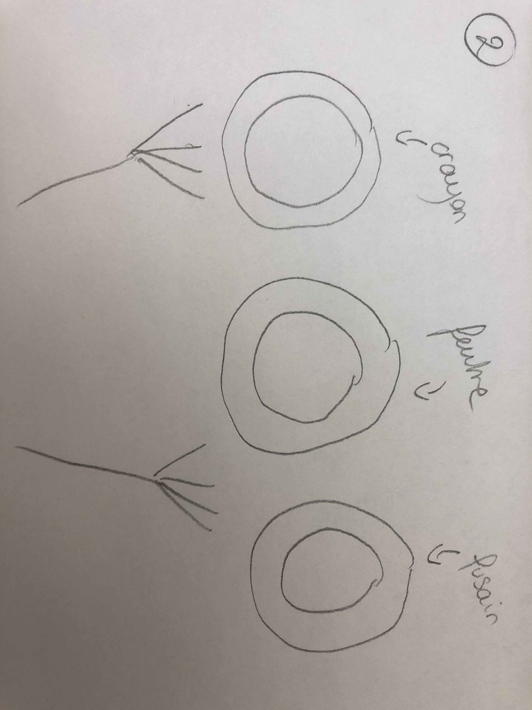
process/2023-11-15/F52EEC8F-537B-4D7C-88F3-462B25EA2E29.jpeg
