oserratr/head-md-caran-ache-project/process/2023-11-15/IMG_32153.png

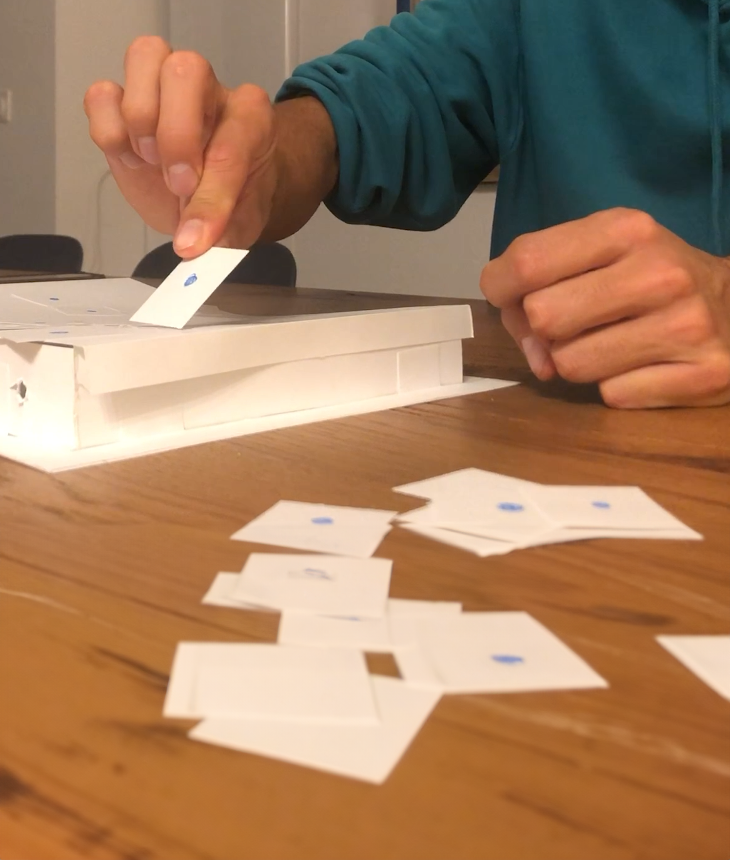
process/2023-11-15/IMG_32153.png
