oserratr/head-md-caran-ache-project/process/2023-11-15/Plan de travail 3.png

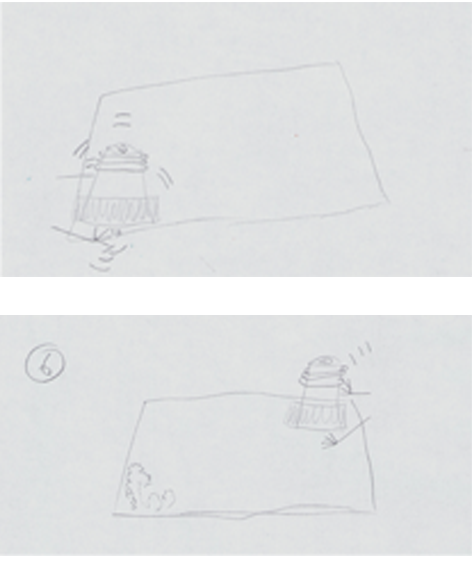
process/2023-11-15/Plan de travail 3.png
