oserratr/head-md-caran-ache-project/process/2023-11-27 a 2023-11-29/4267D3E0-D222-4316-B545-1FBA8A3AAC2E.jpeg

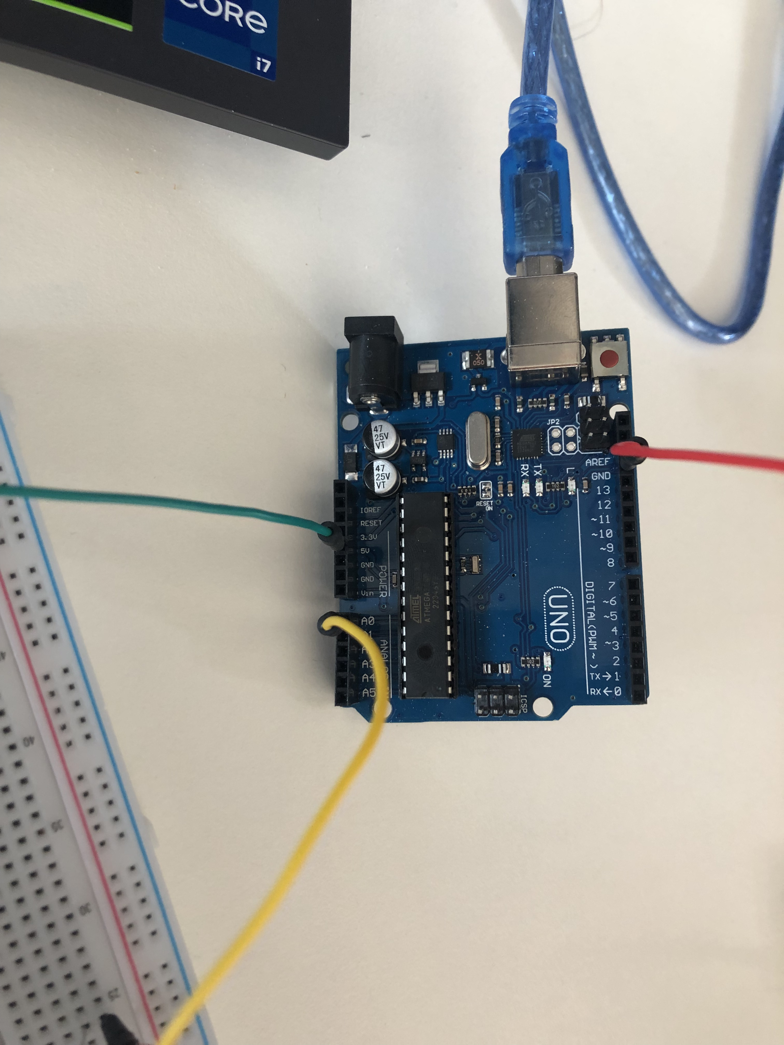
process/2023-11-27 a 2023-11-29/4267D3E0-D222-4316-B545-1FBA8A3AAC2E.jpeg
