oserratr/head-md-caran-ache-project/process/2023-11-27 a 2023-11-29/C31BB5E2-3799-479D-B31E-92B5CF7547DC.jpeg

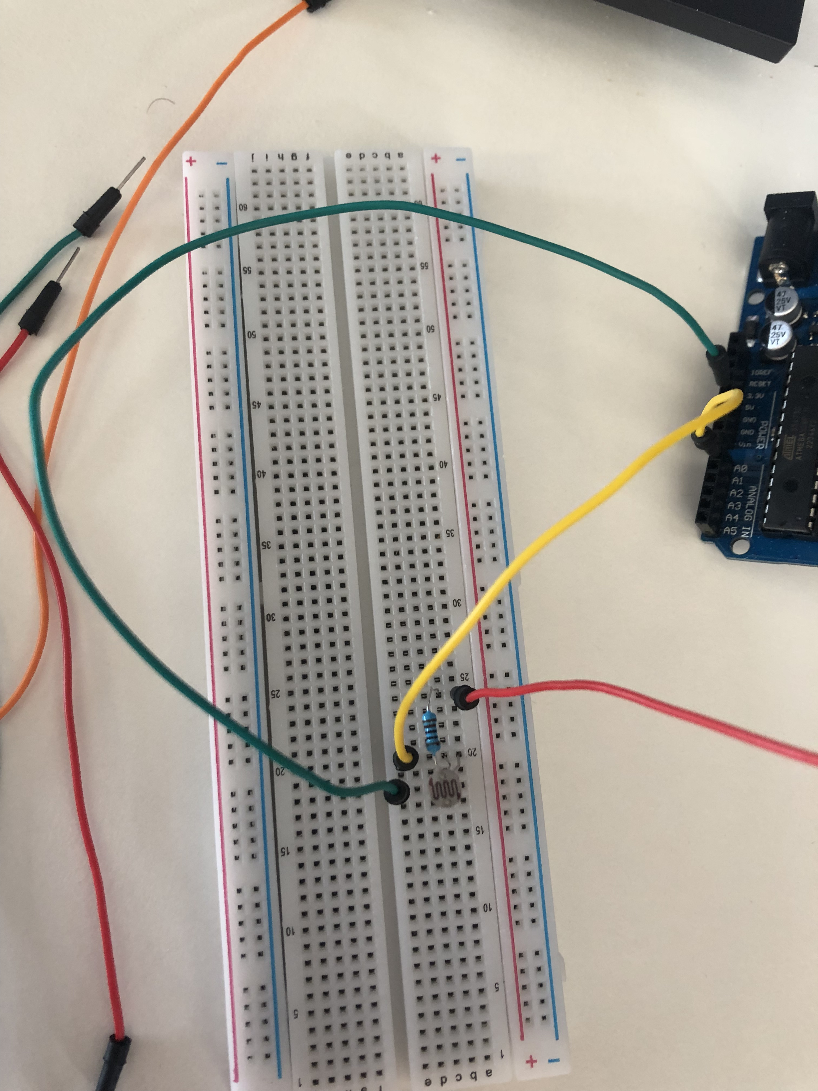
process/2023-11-27 a 2023-11-29/C31BB5E2-3799-479D-B31E-92B5CF7547DC.jpeg
