oserratr/head-md-caran-ache-project/process/2023-11-27 a 2023-11-29/D08A829C-56A8-4EBA-BE1E-DBAA905DD2F6.jpeg

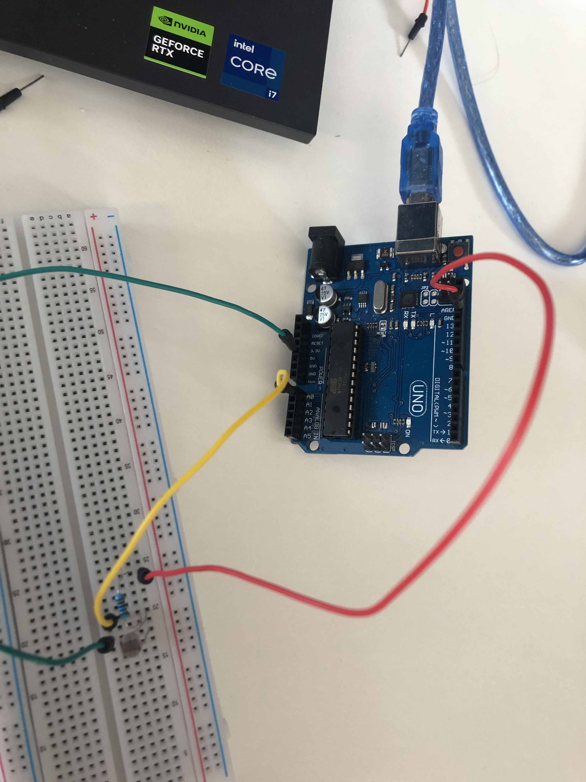
process/2023-11-27 a 2023-11-29/D08A829C-56A8-4EBA-BE1E-DBAA905DD2F6.jpeg
