oserratr/head-md-caran-ache-project/process/2023-12-14/IMG_0447.jpg

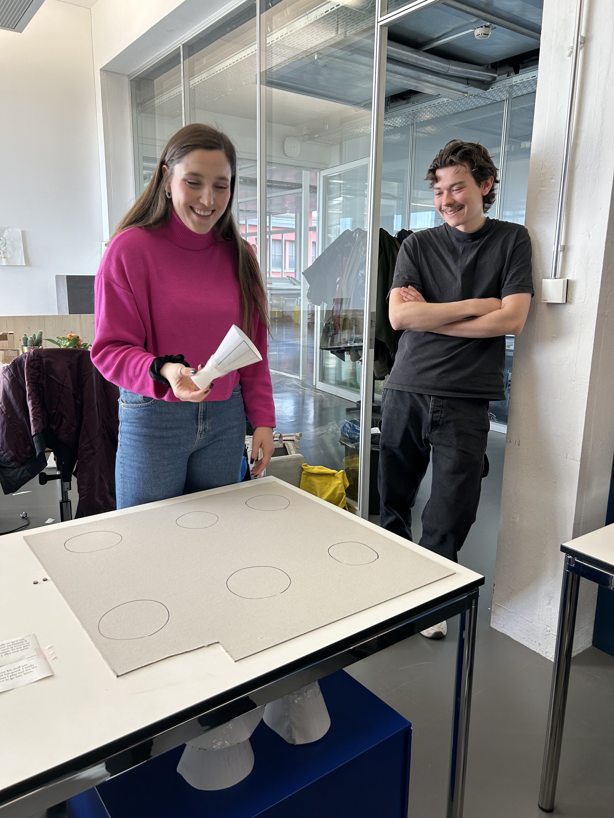
process/2023-12-14/IMG_0447.jpg
