oserratr/head-md-caran-ache-project/process/2023-12-14/IMG_0448.jpg

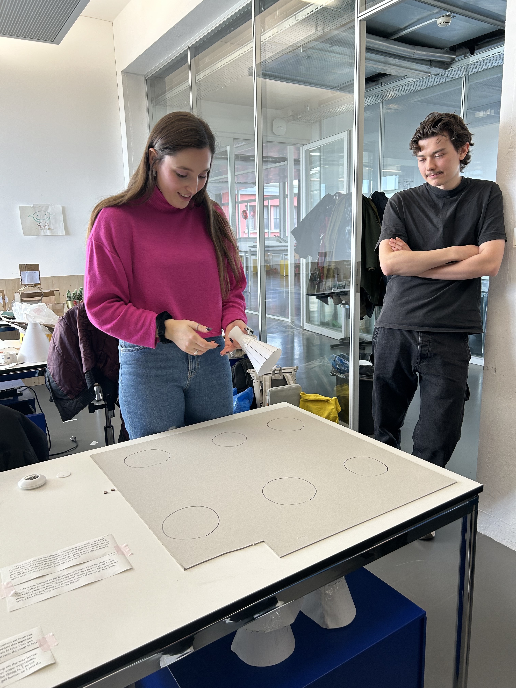
process/2023-12-14/IMG_0448.jpg
