oserratr/head-md-caran-ache-project/process/2023-12-14/IMG_0449 (1).jpg

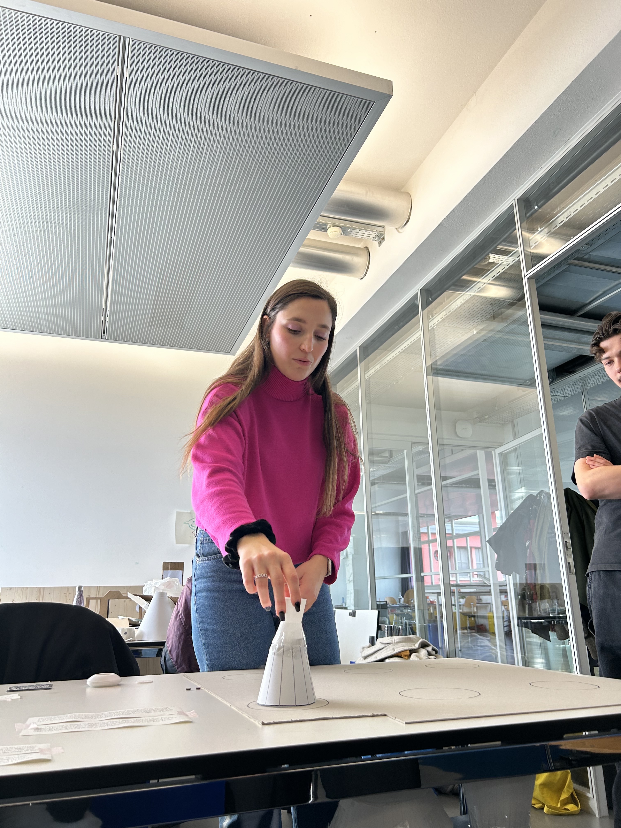
process/2023-12-14/IMG_0449 (1).jpg
