oserratr/head-md-caran-ache-project/process/2023-12-14/IMG_0452.jpg

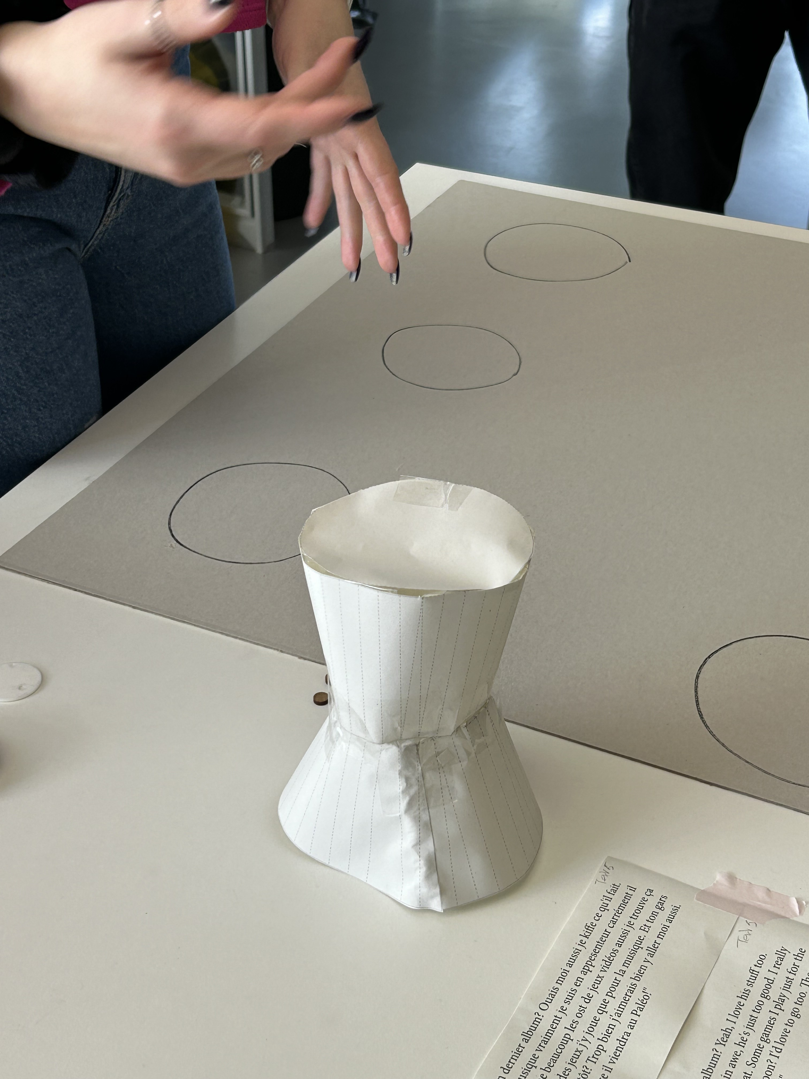
process/2023-12-14/IMG_0452.jpg
