oserratr/head-md-caran-ache-project/process/2023-12-14/IMG_0454.jpg

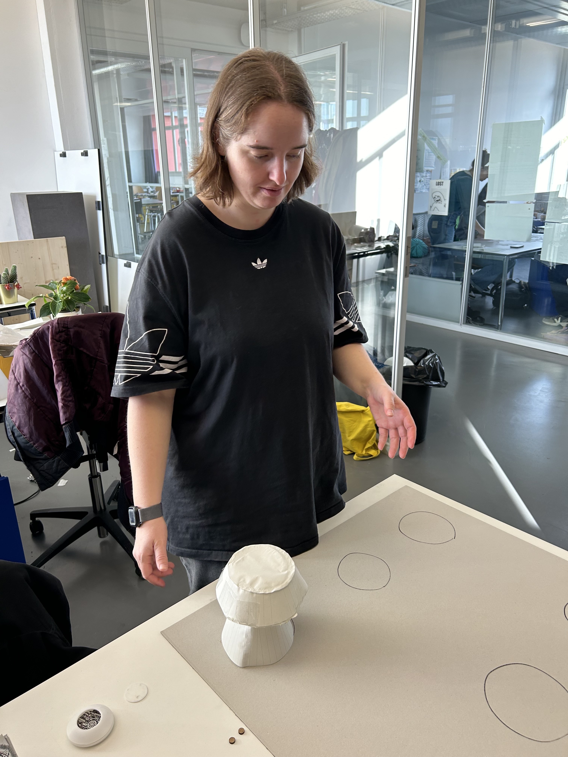
process/2023-12-14/IMG_0454.jpg
