oserratr/head-md-caran-ache-project/process/2024-01-16/foret/1.png

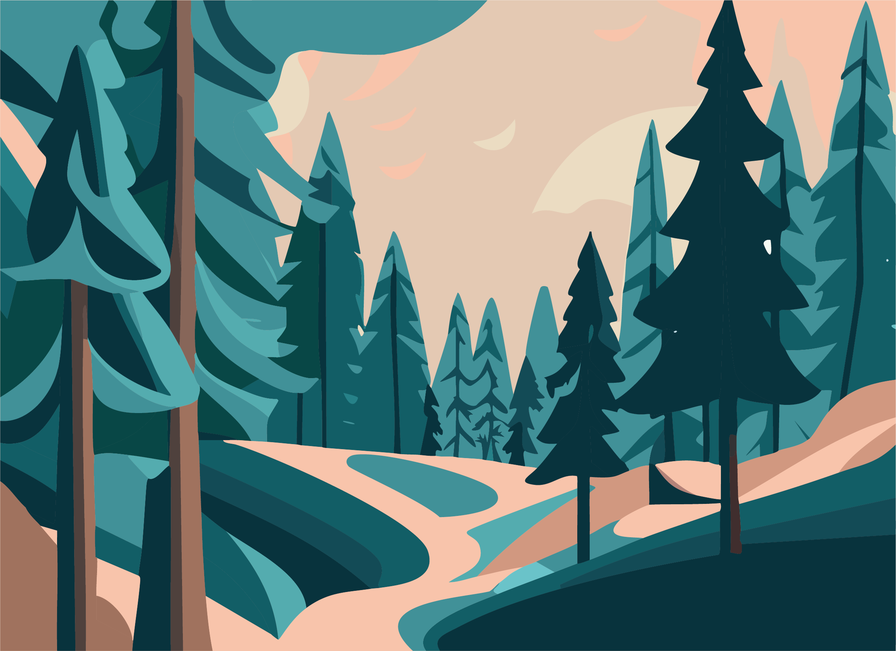
process/2024-01-16/foret/1.png
