oserratr/head-md-caran-ache-project/process/2024-01-16/foret/2.png

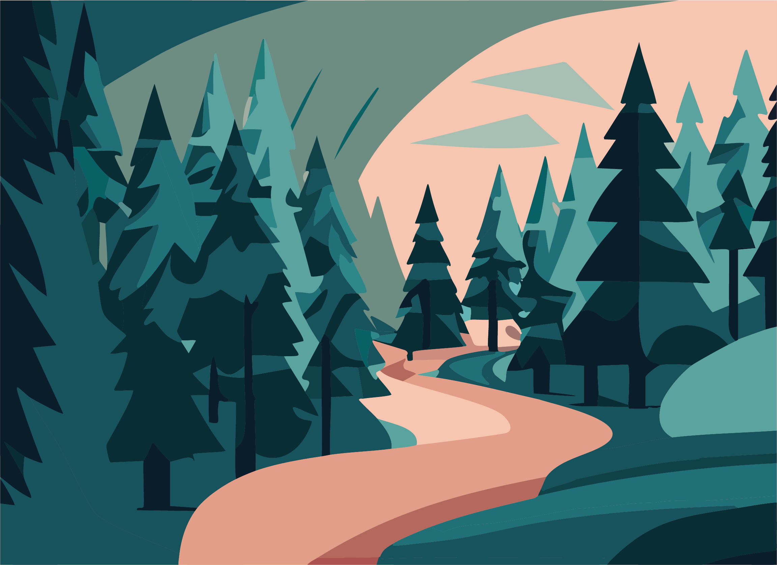
process/2024-01-16/foret/2.png
