oserratr/head-md-caran-ache-project/process/2024-01-16/mer/1.png

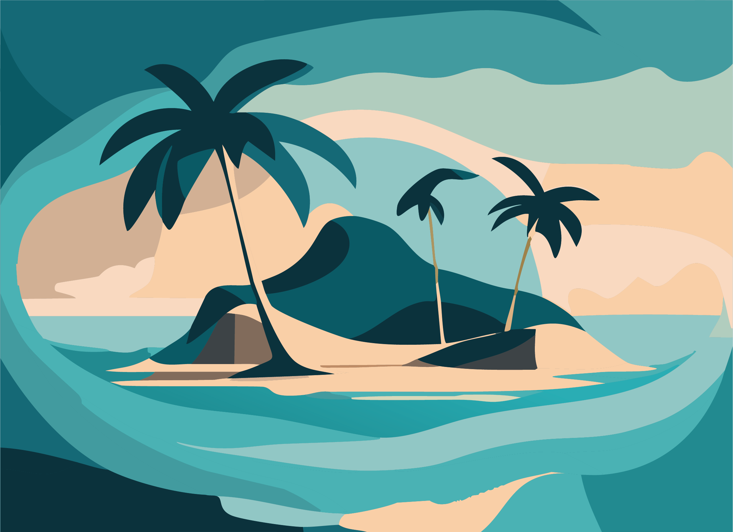
process/2024-01-16/mer/1.png
