oserratr/head-md-caran-ache-project/process/2024-01-16/presentation/part1.png

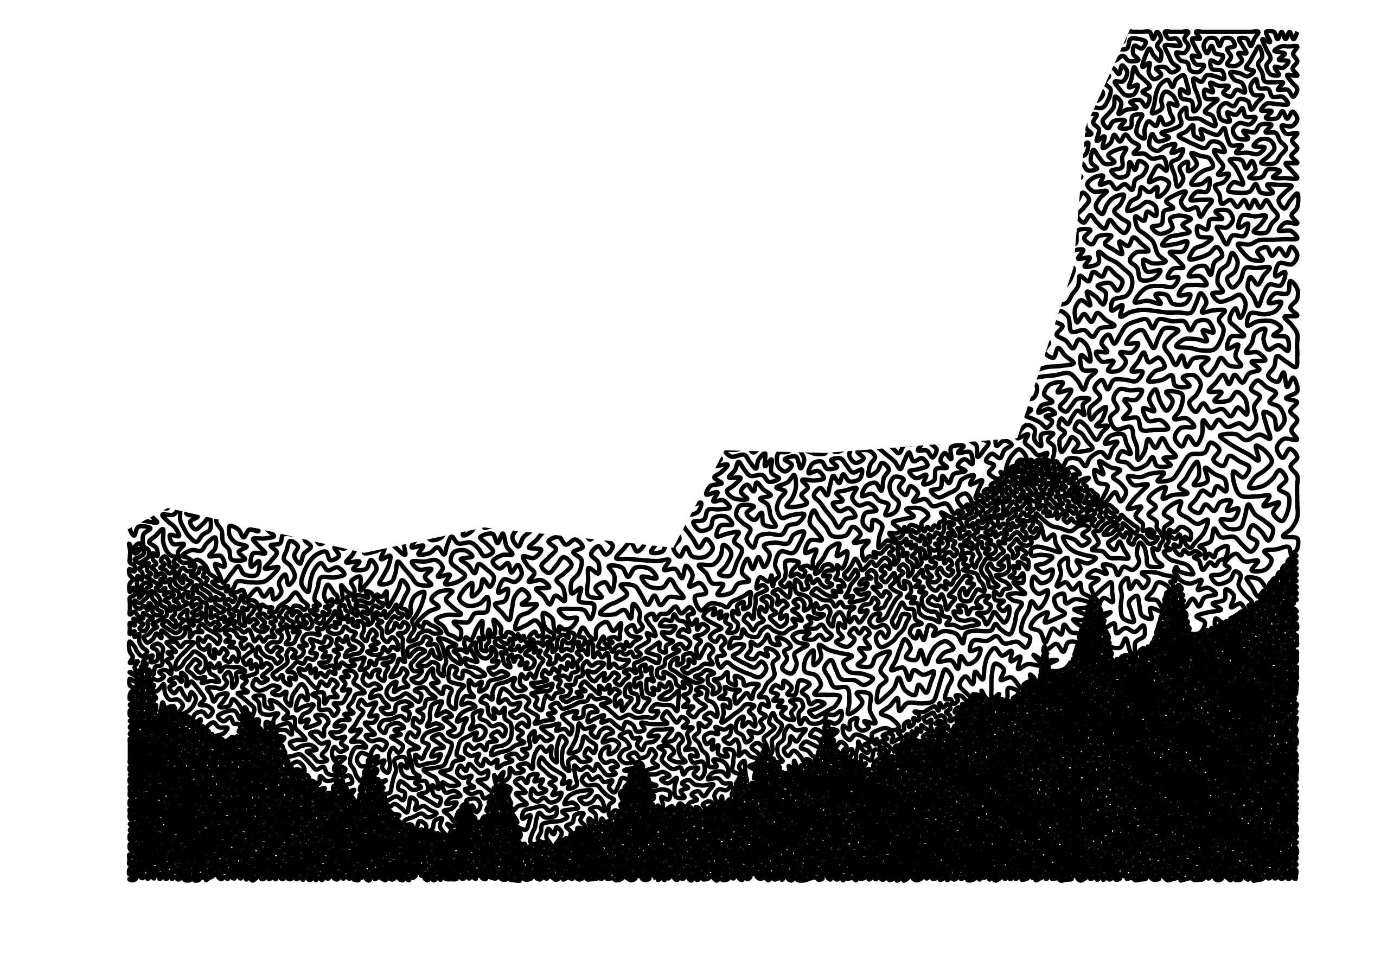
process/2024-01-16/presentation/part1.png
