oserratr/head-md-caran-ache-project/process/2023-12-04/material.jpg

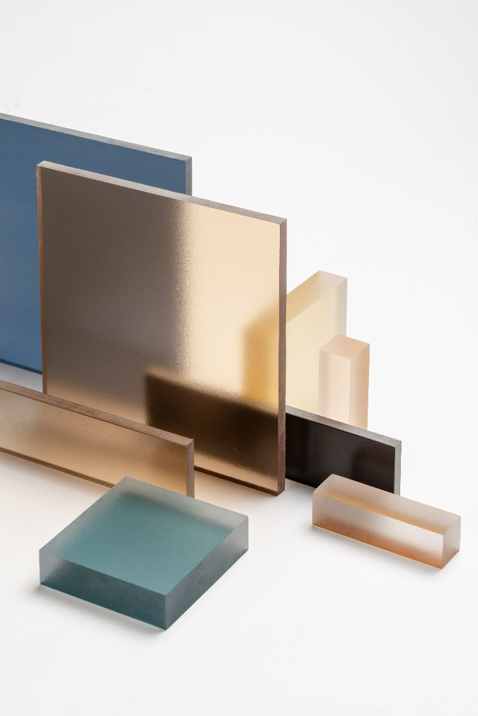
process/2023-12-04/material.jpg
