oserratr/head-md-caran-ache-project/form/2023-12-12/print3d-forme1v3.jpg

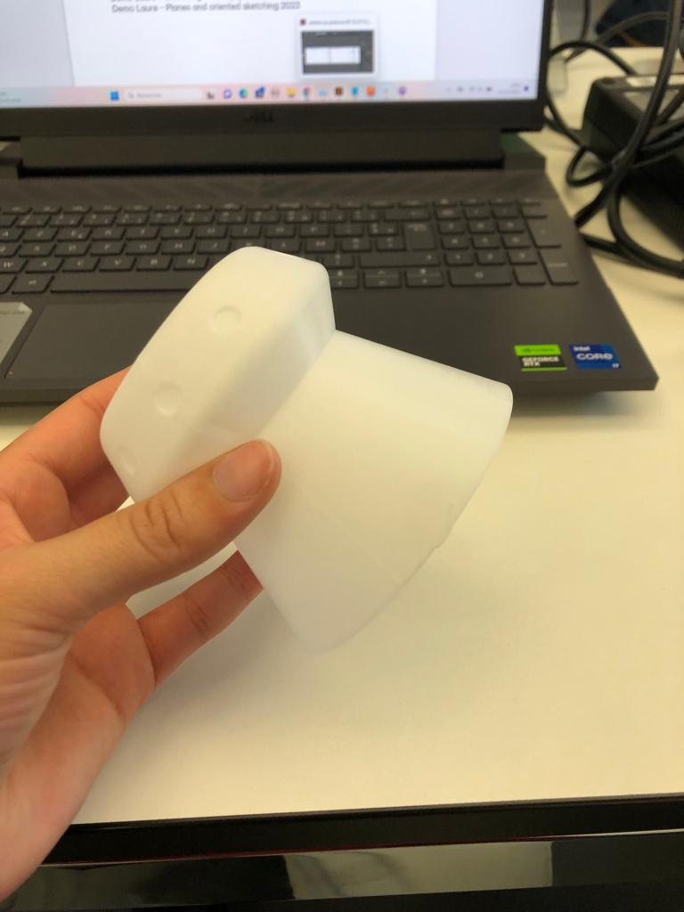
form/2023-12-12/print3d-forme1v3.jpg
