oserratr/head-md-caran-ache-project/form/2023-12-12/print3d-forme2v2.jpg

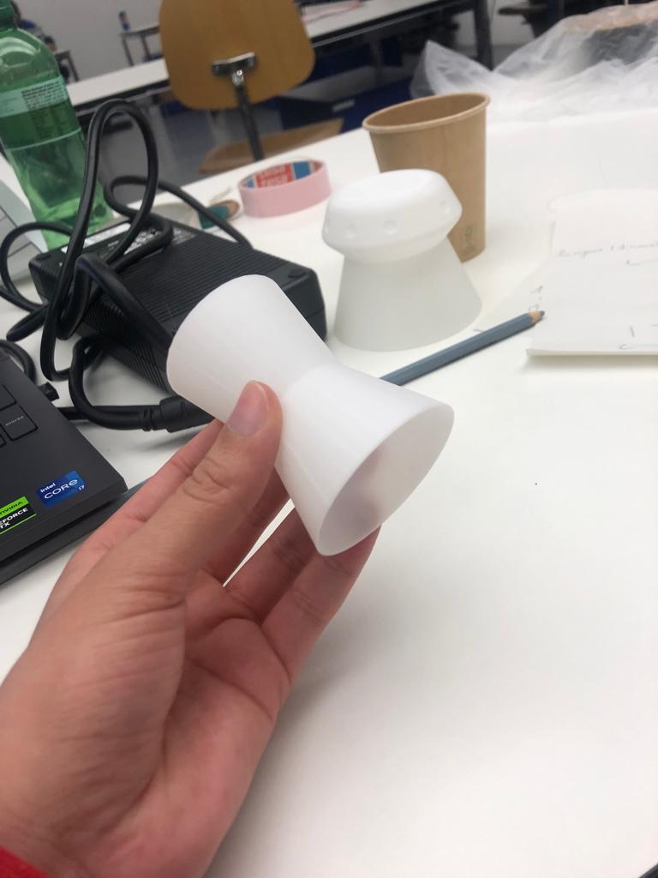
form/2023-12-12/print3d-forme2v2.jpg
