oserratr/head-md-caran-ache-project/process/2023-11-07/constructions-pieces.png

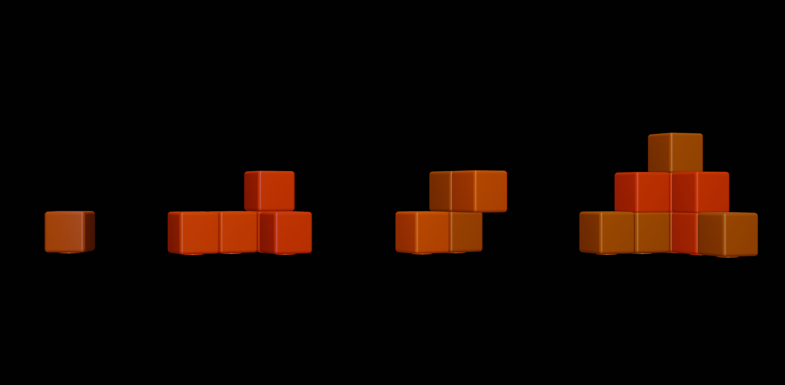
process/2023-11-07/constructions-pieces.png
