oserratr/head-md-caran-ache-project/electronics/2023-12-05/test-vibration-switc/set-vibration-sensor.jpg

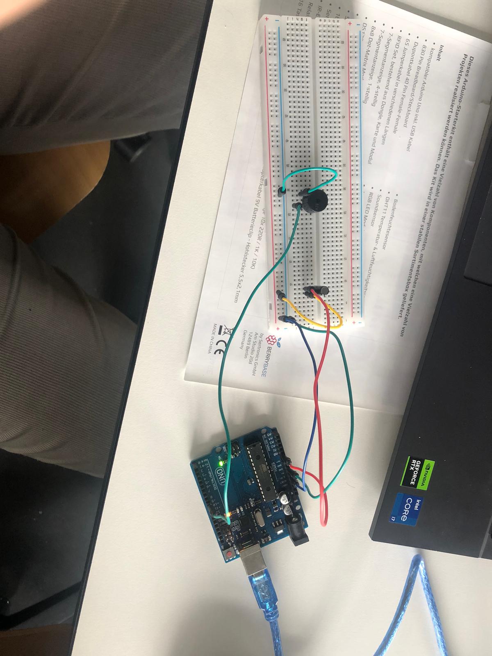
electronics/2023-12-05/test-vibration-switc/set-vibration-sensor.jpg
