oserratr/head-md-caran-ache-project/electronics/2023-12-20/rfid test.jpg

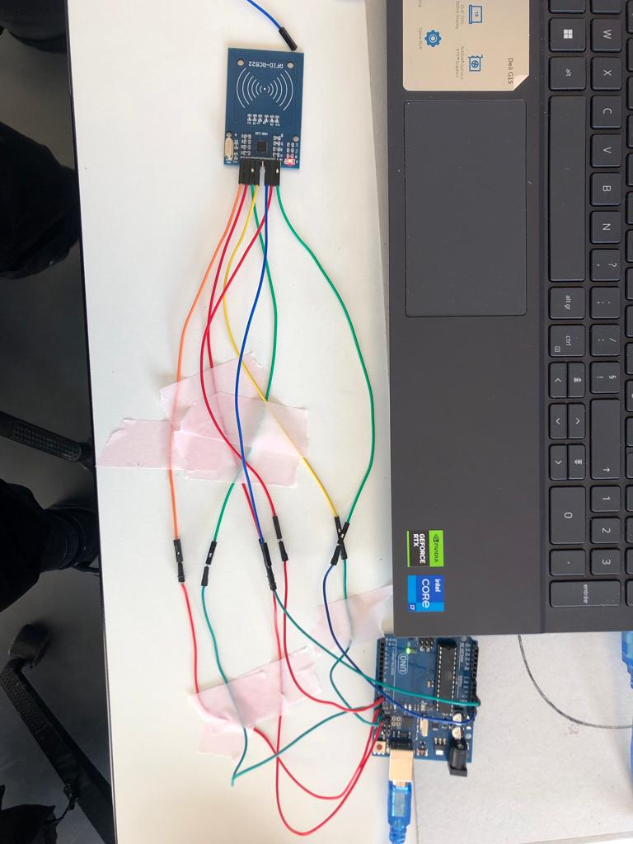
electronics/2023-12-20/rfid test.jpg
