oserratr/head-md-caran-ache-project/electronics/2024-01-09/send_bt_mouse_esp32/data/1/test.jpg

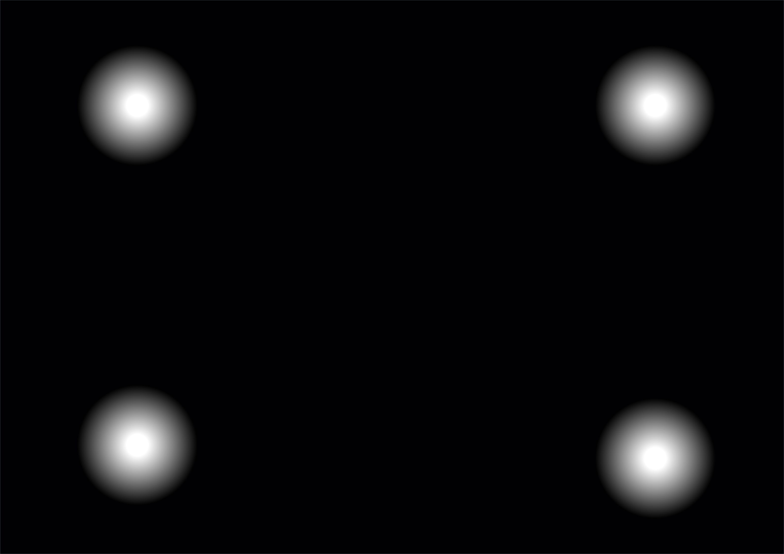
electronics/2024-01-09/send_bt_mouse_esp32/data/1/test.jpg
