oserratr/head-md-caran-ache-project/process/2023-11-12/dessin-test-proto-2 (1).png

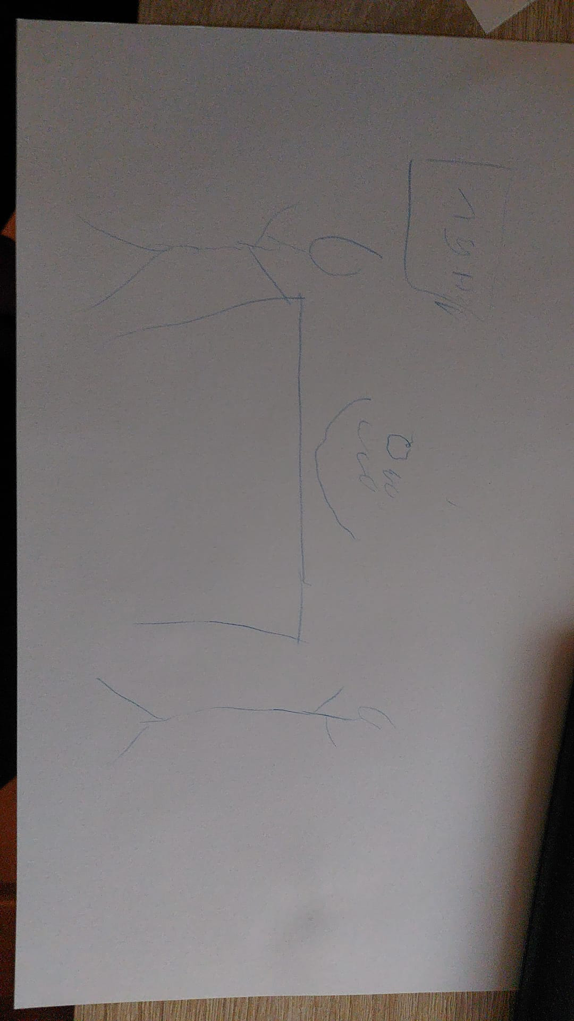
process/2023-11-12/dessin-test-proto-2 (1).png
