oserratr/head-md-caran-ache-project/process/2023-11-13/test proto paysage.png

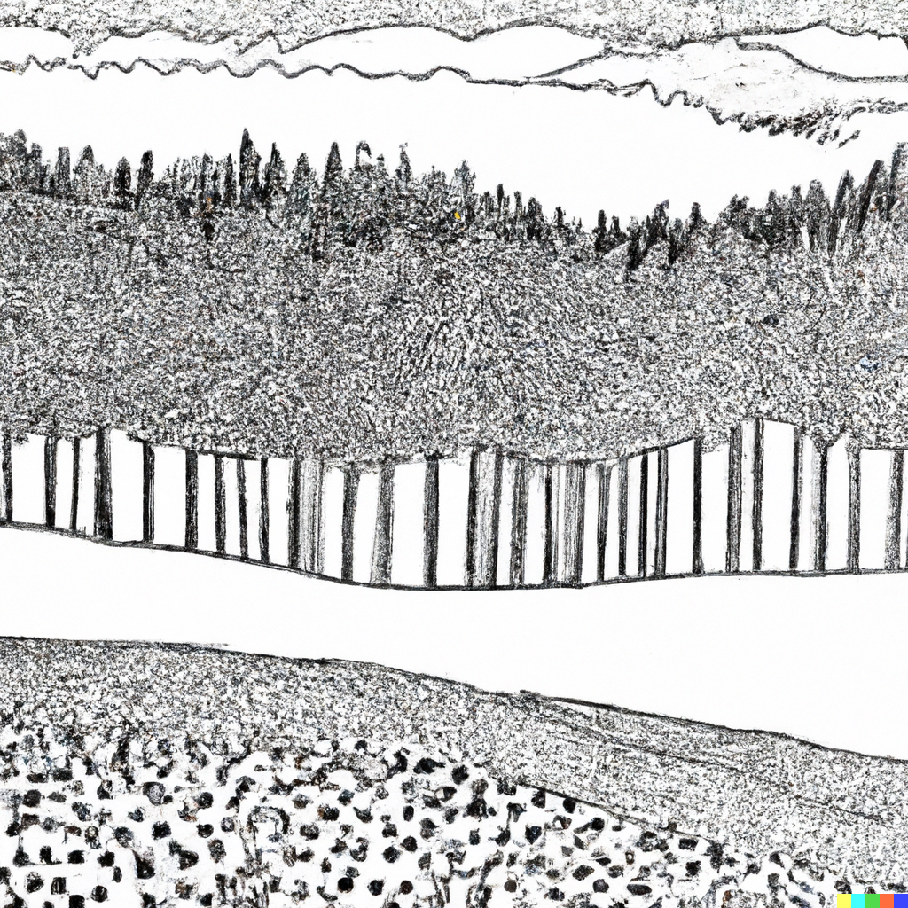
process/2023-11-13/test proto paysage.png
