oserratr/head-md-caran-ache-project/form/2024-01-10/plan-drawing.pdf

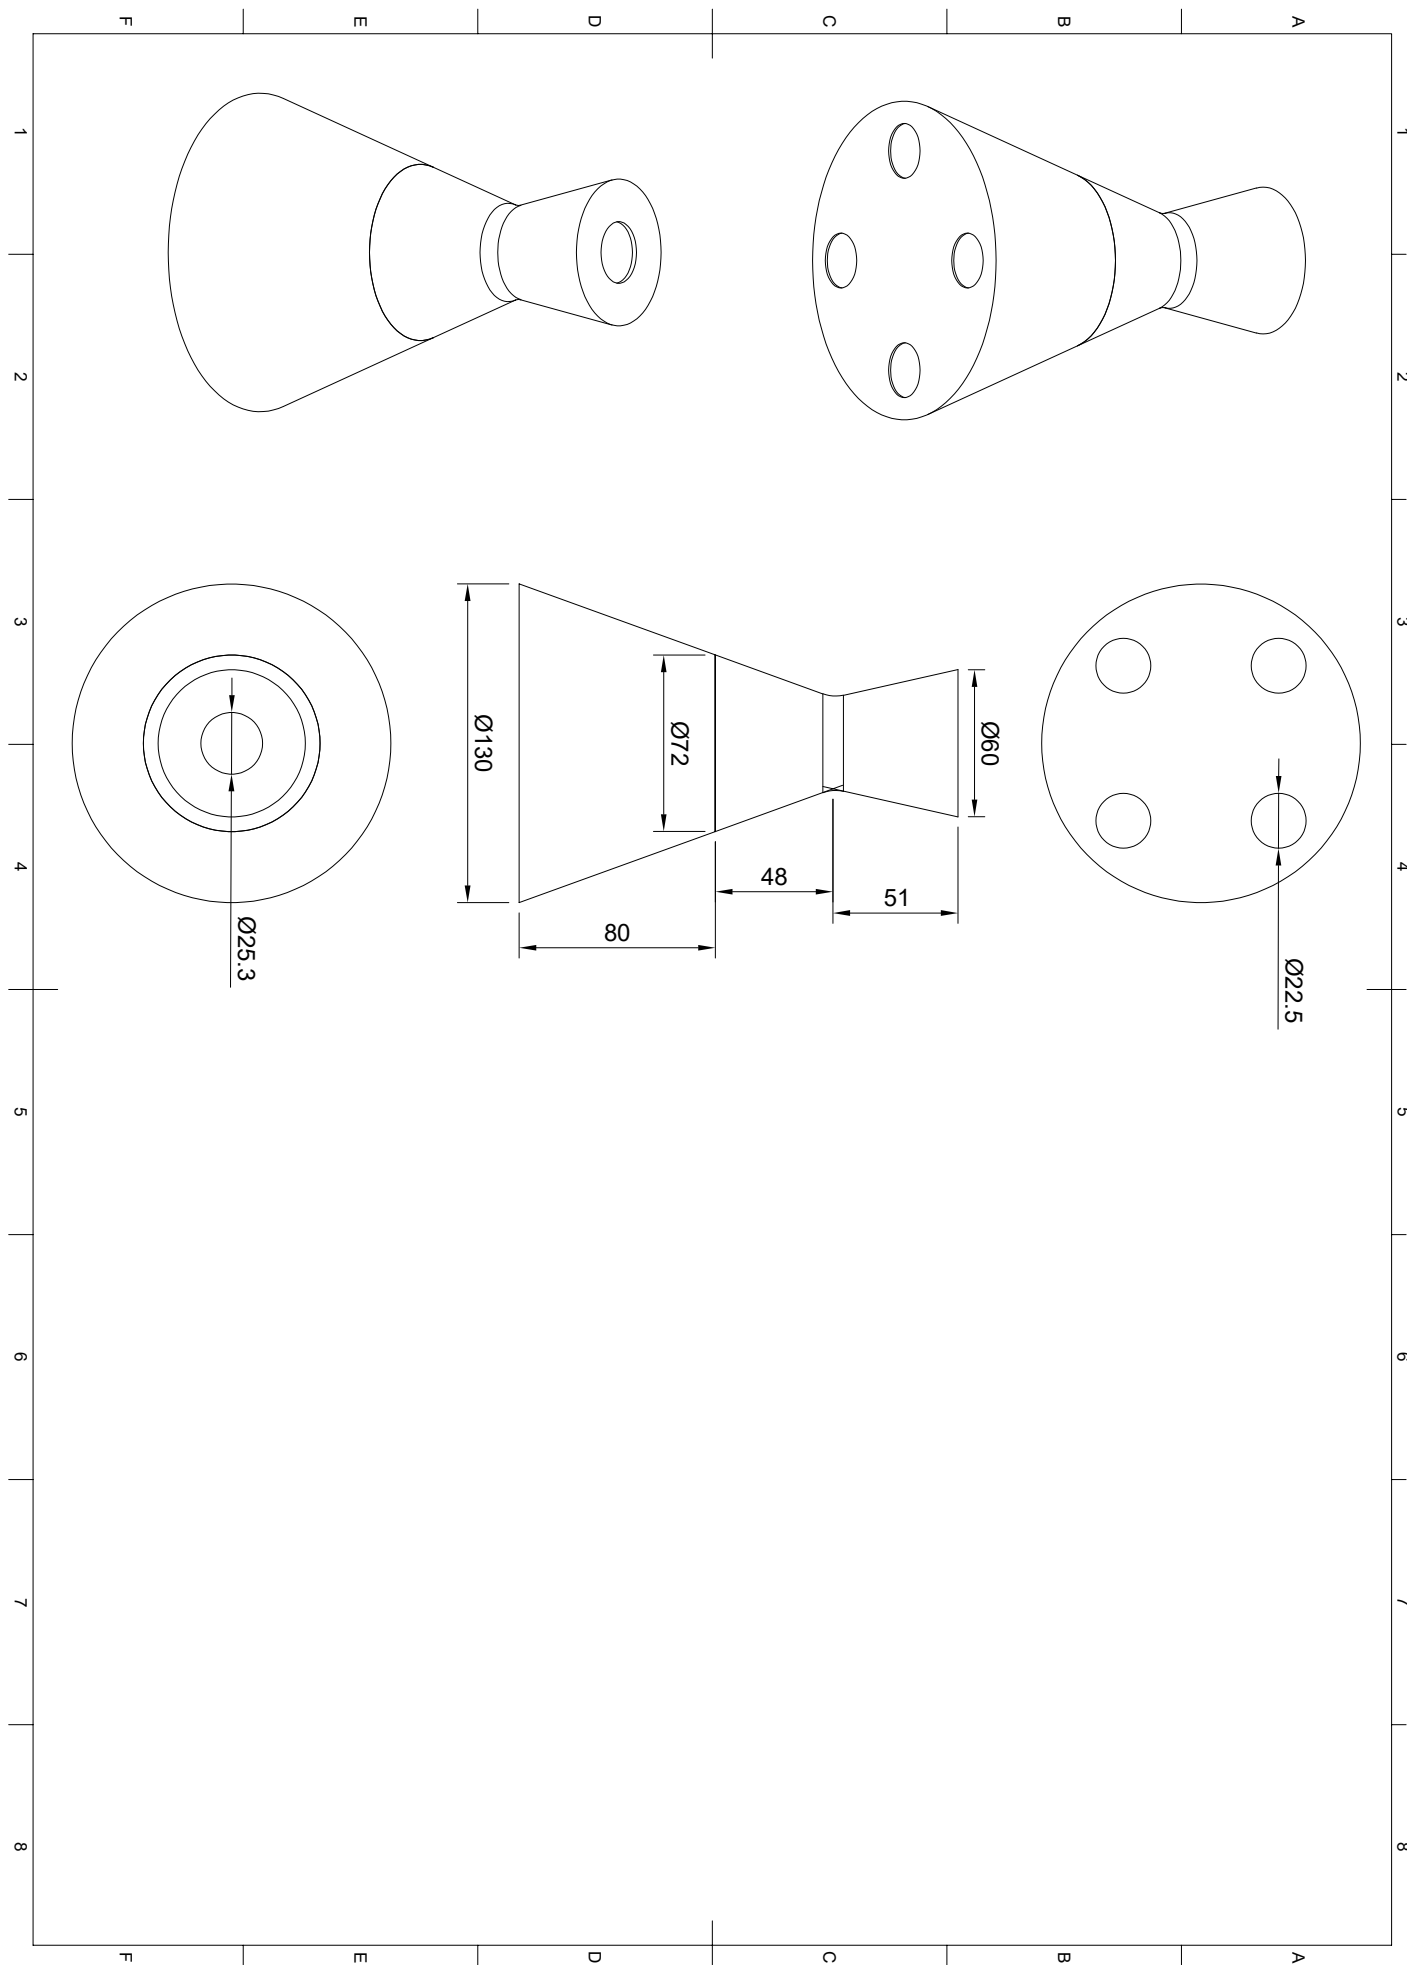
[picture p205: page 1]
1 A 2 3 4 5 6 7 8 1 2 3 4 5 6 7 8 FEDCB FEDCBA Ø130 Ø72 Ø60 Ø22.5 Ø25.3
