oserratr/head-md-caran-ache-project/form/2023-12-12/forme1.pdf

## Dimensions, matériaux, forme objet 1, prise a une main

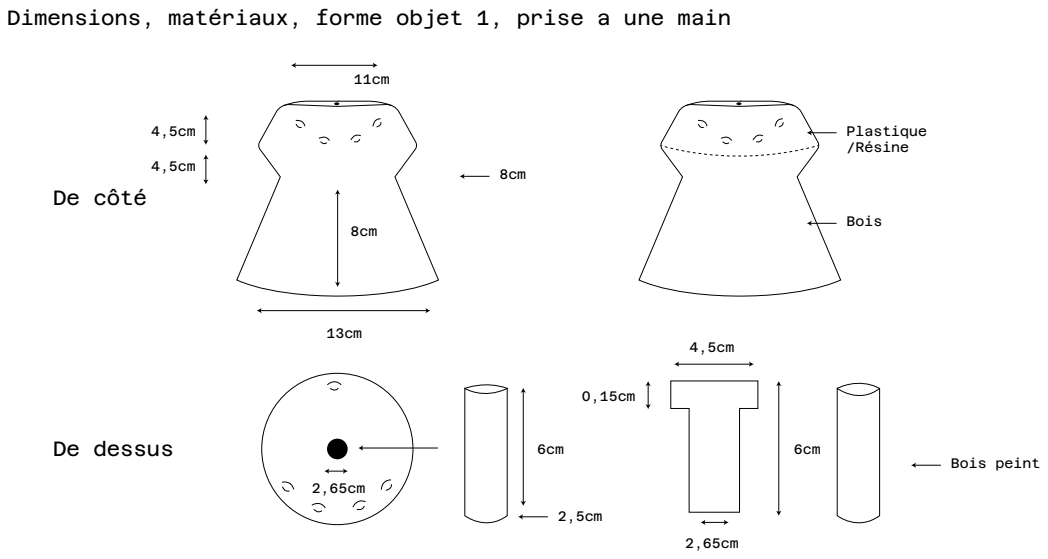
[picture p206: page 1]
De côté; De dessus; Bois; Bois peint; Plastique /Résine
