oserratr/head-md-caran-ache-project/form/2023-12-12/forme2.pdf

## Dimensions, matériaux, forme objet 2, prise a 2 mains

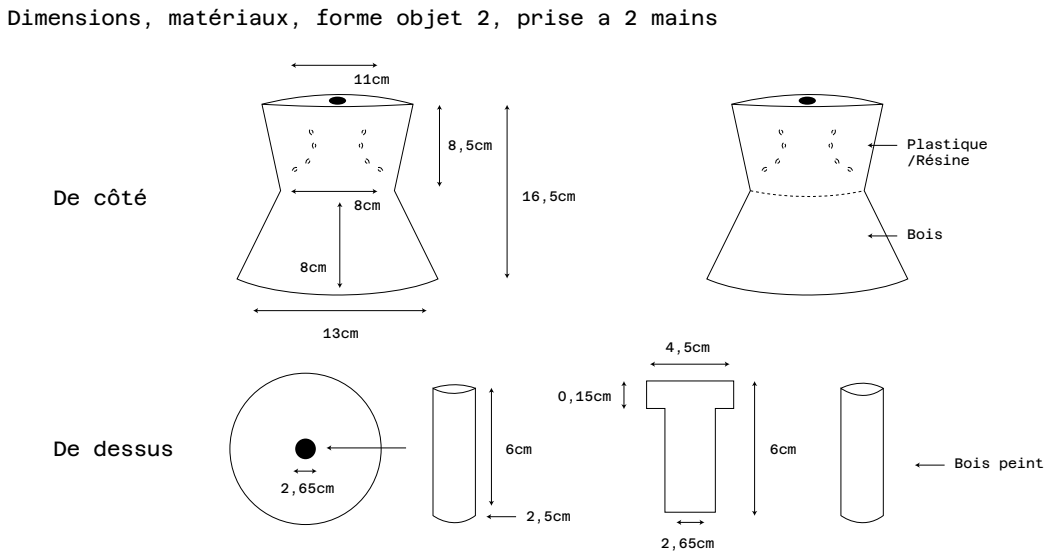
[picture p207: page 1]
De côté; De dessus; Bois peint; Bois; Plastique /Résine
