oserratr/head-md-caran-ache-project/form/2023-12-12/forme3.pdf

## Dimensions, matériaux, forme objet 3, prise a 1 ou 2 mains

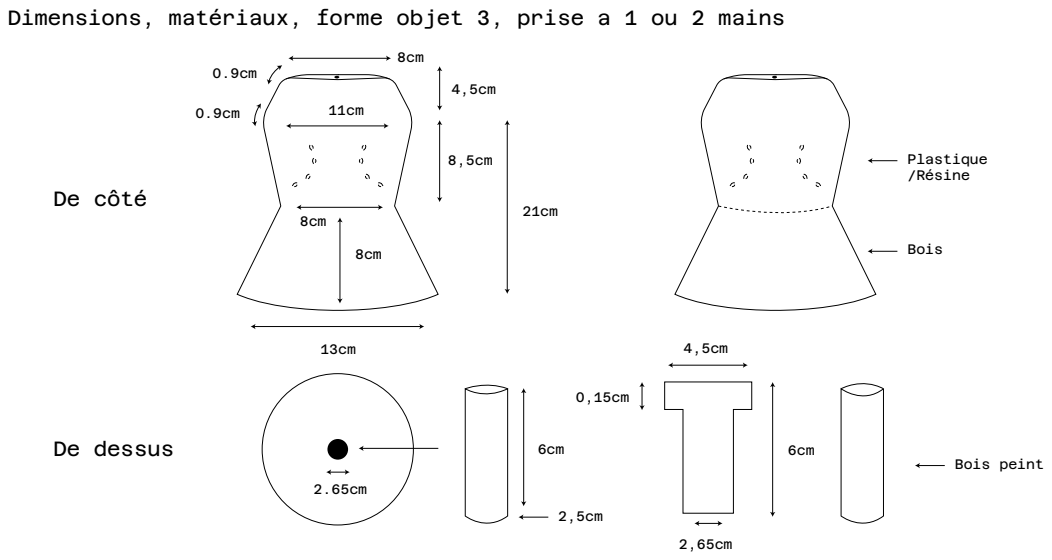
[picture p208: page 1]
De côté; De dessus; Bois peint; Bois; Plastique /Résine
