oserratr/head-md-caran-ache-project/form/2023-12-12/forme4.pdf

## Dimensions, matériaux, forme objet 4, prise a 1 ou 2 mains

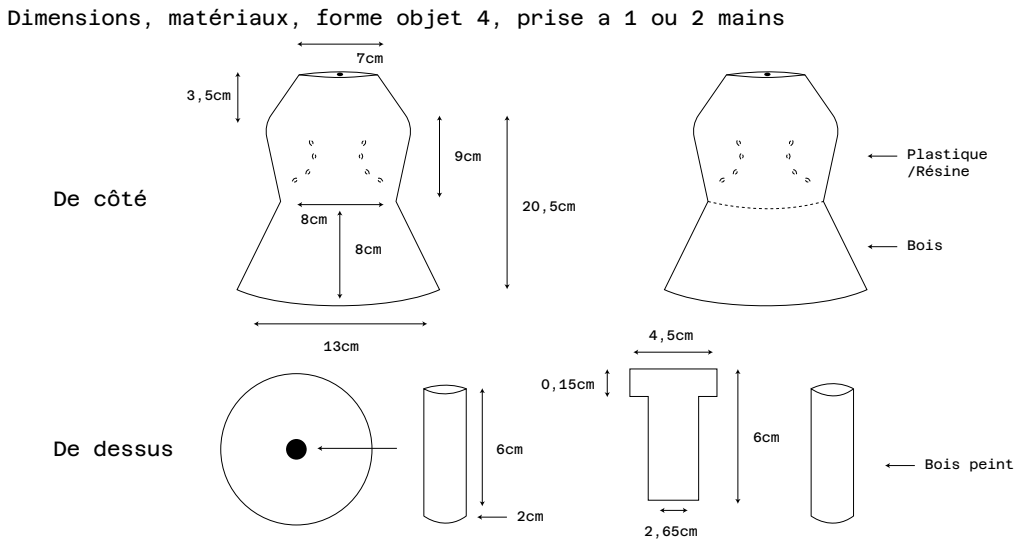
[picture p209: page 1]
De côté; De dessus; Bois peint; Bois; Plastique /Résine
