oserratr/head-md-caran-ache-project/form/2023-12-11/forme1.pdf

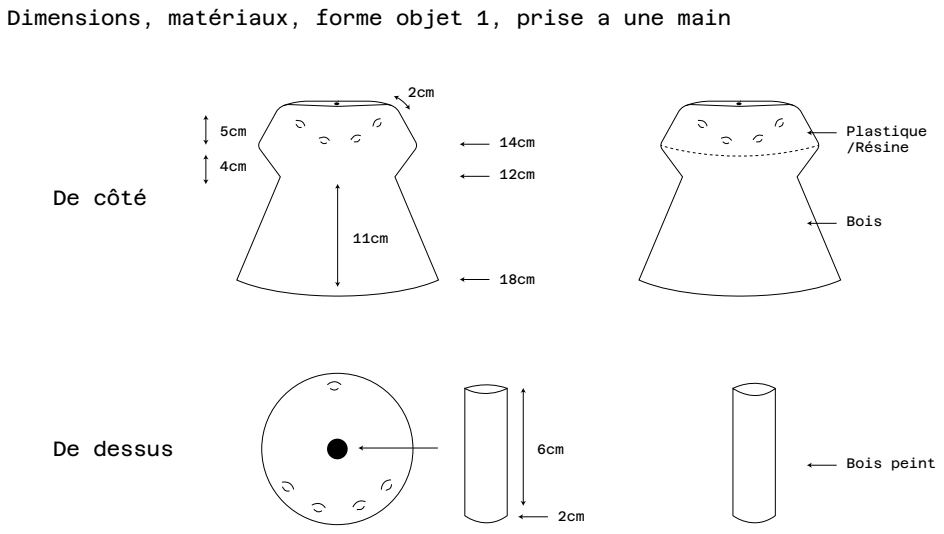
[picture p210: page 1]
De côté; De dessus; Bois; Bois peint; Plastique /Résine

Dimensions, matériaux, forme objet 1, prise a une main
