oserratr/head-md-caran-ache-project/process/2023-10-20/pistes.pdf

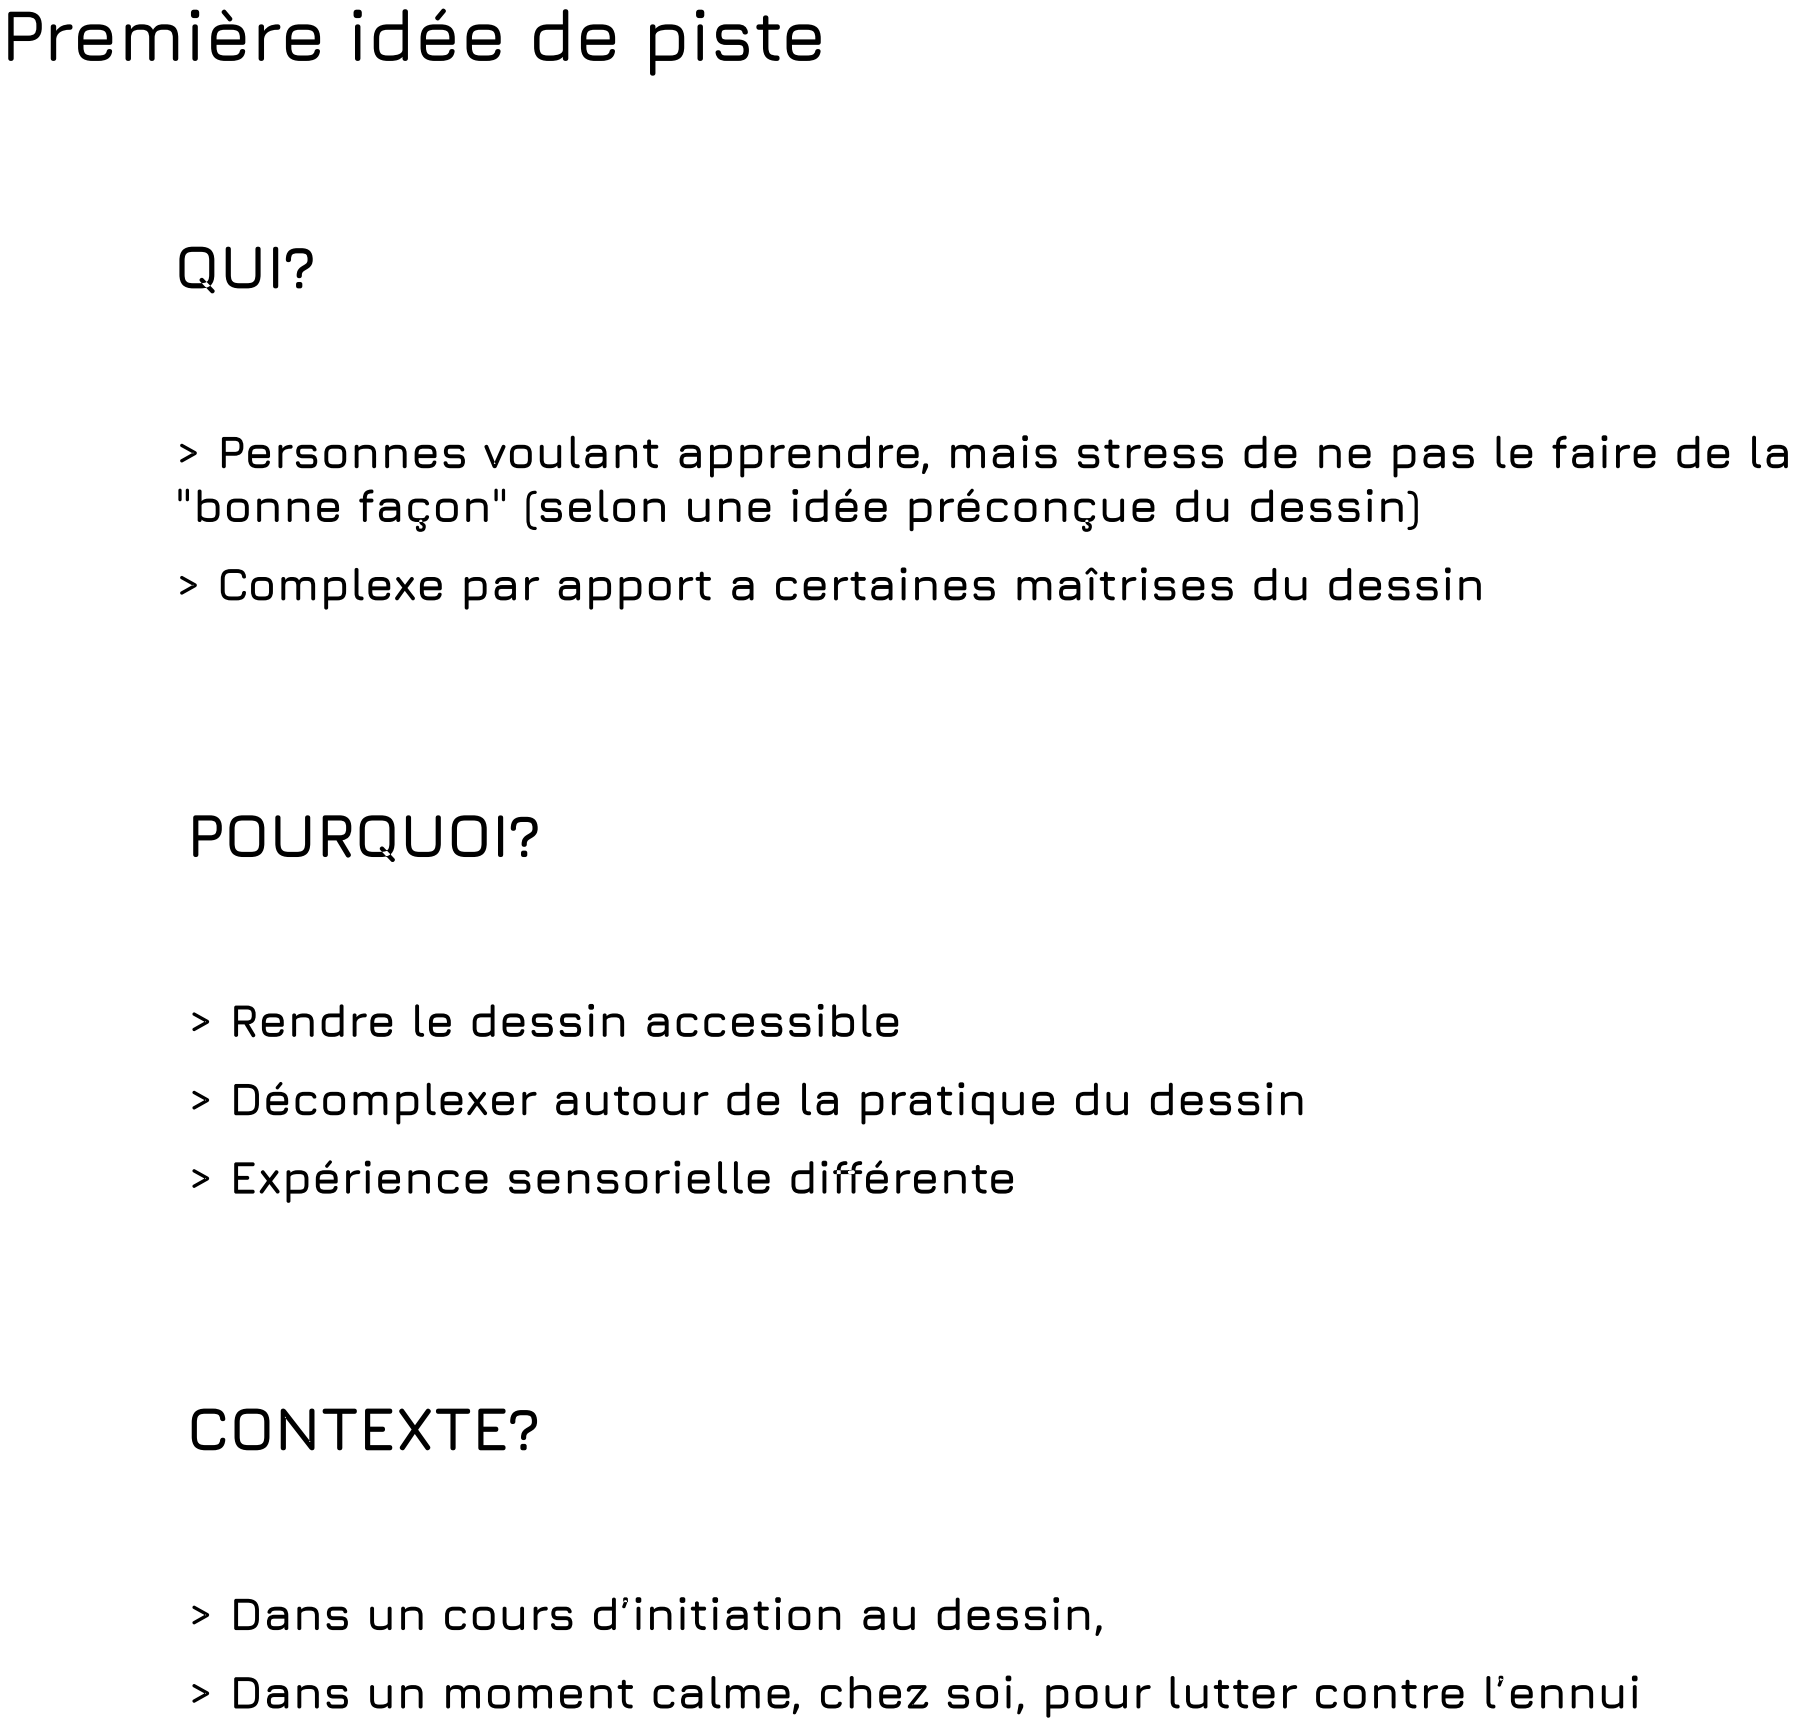
[picture p211: page 1]
