oserratr/head-md-caran-ache-project/process/2023-10-20/recherches-en-ligne.pdf

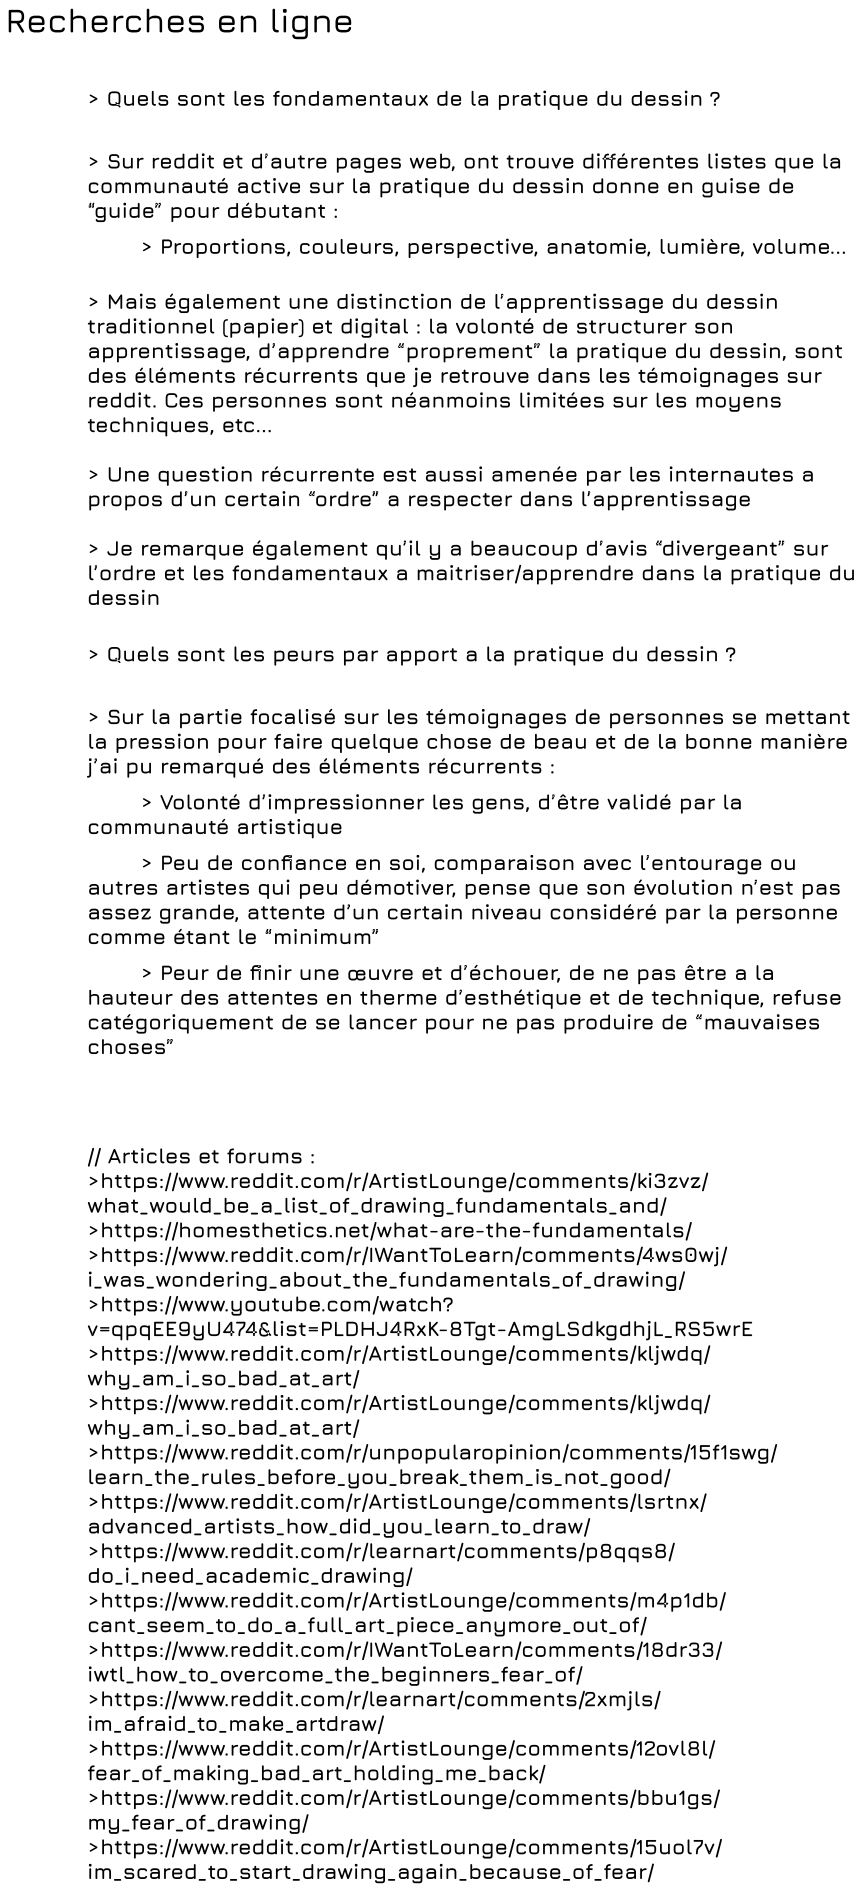
[picture p212: page 1]
