oserratr/head-md-caran-ache-project/process/2024-01-16/presentation/deuxieme.pdf

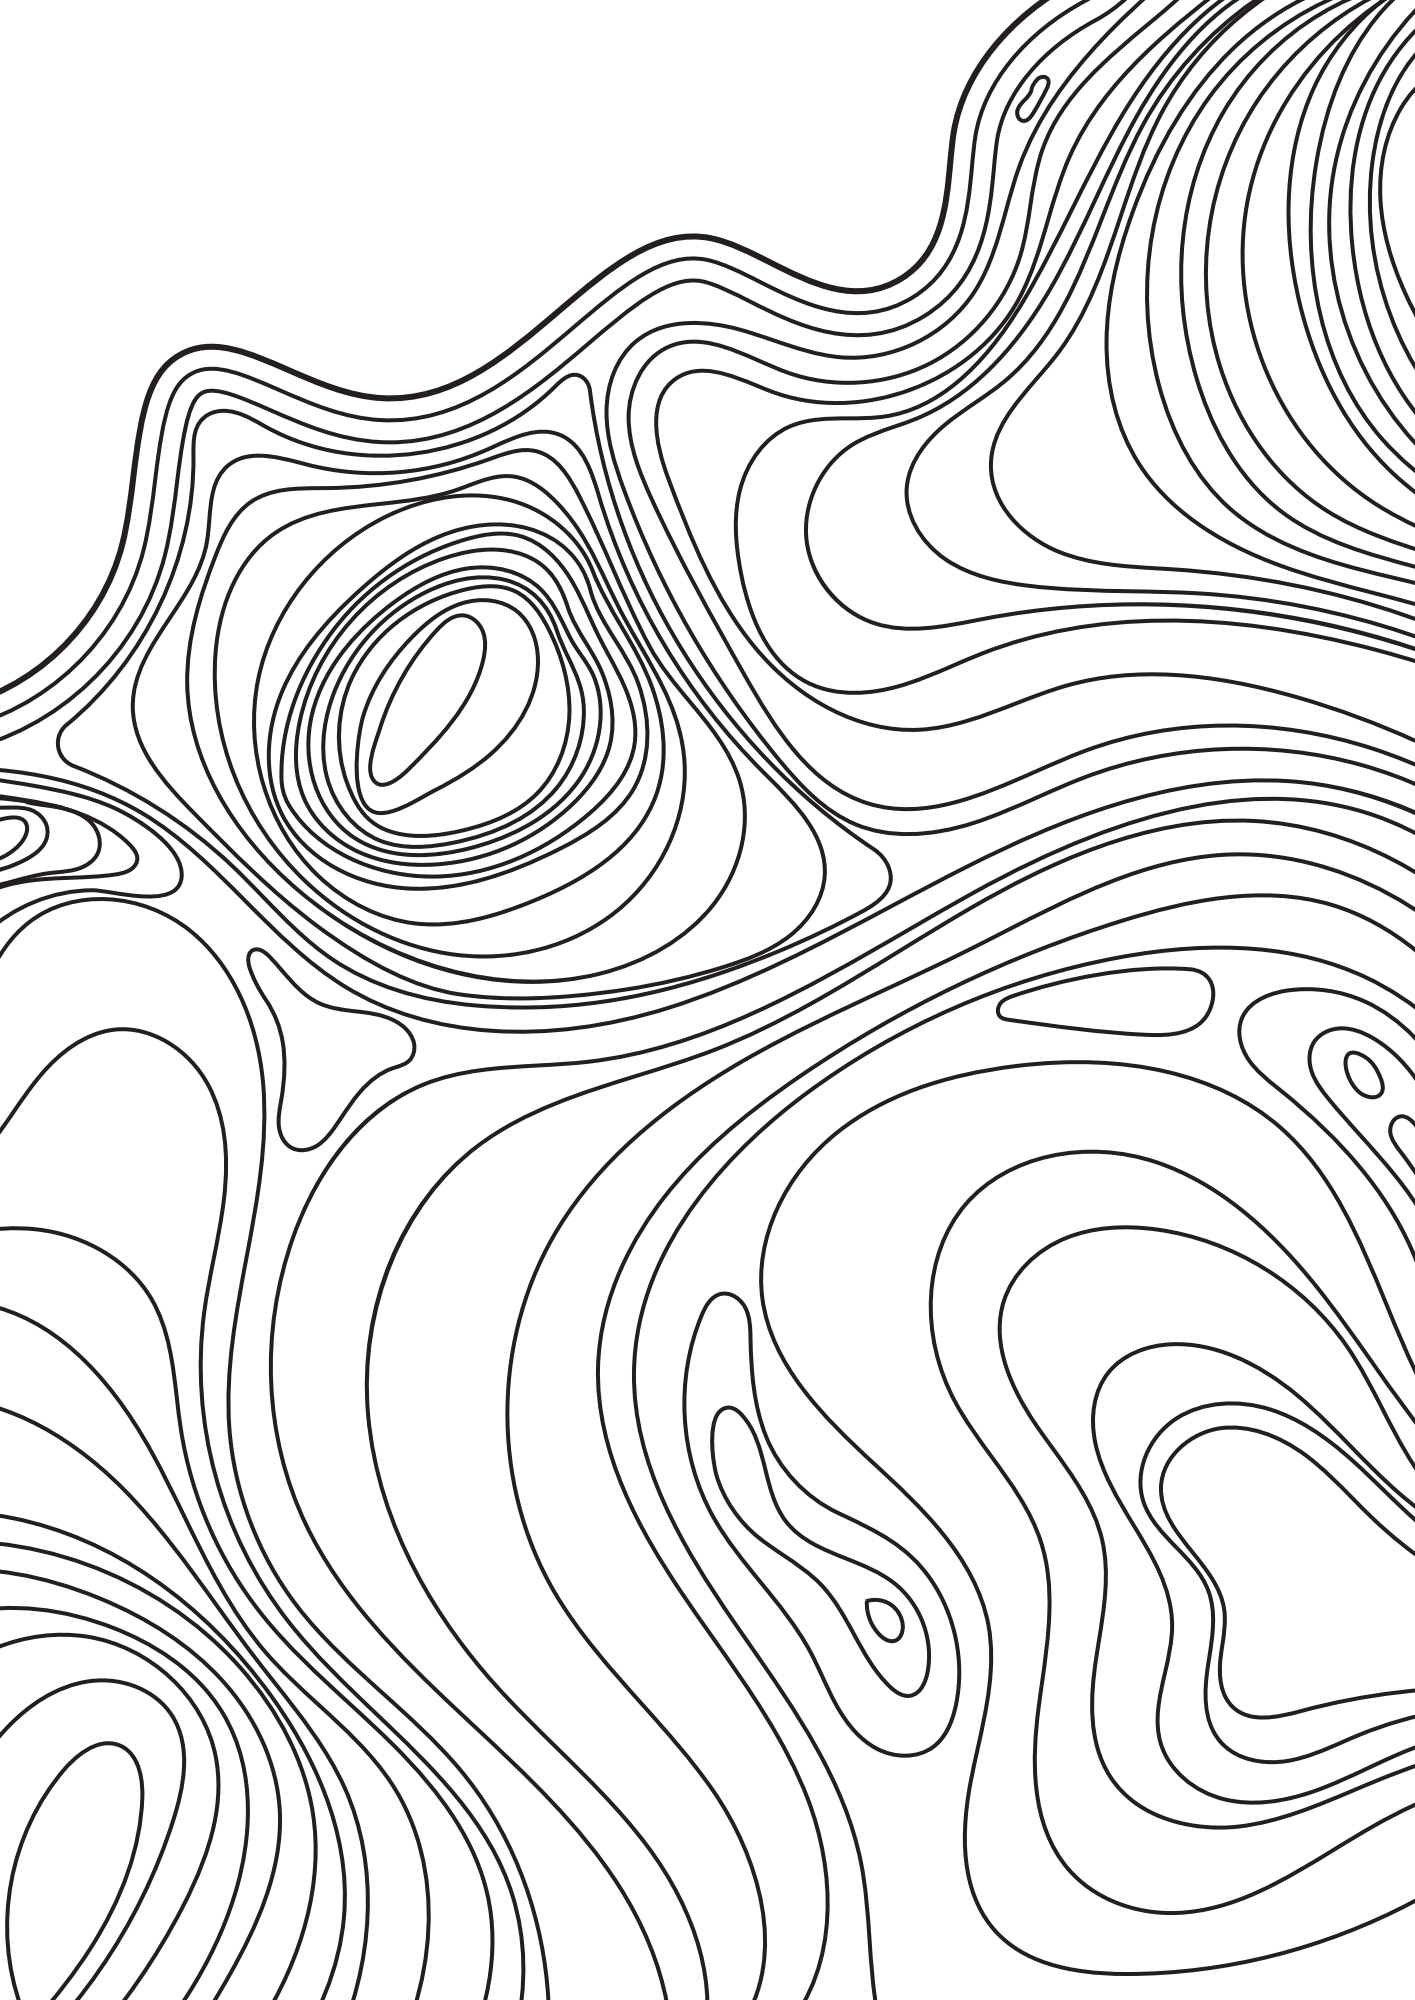
[picture p213: page 1]
