oserratr/head-md-caran-ache-project/process/2024-01-16/presentation/premier.pdf

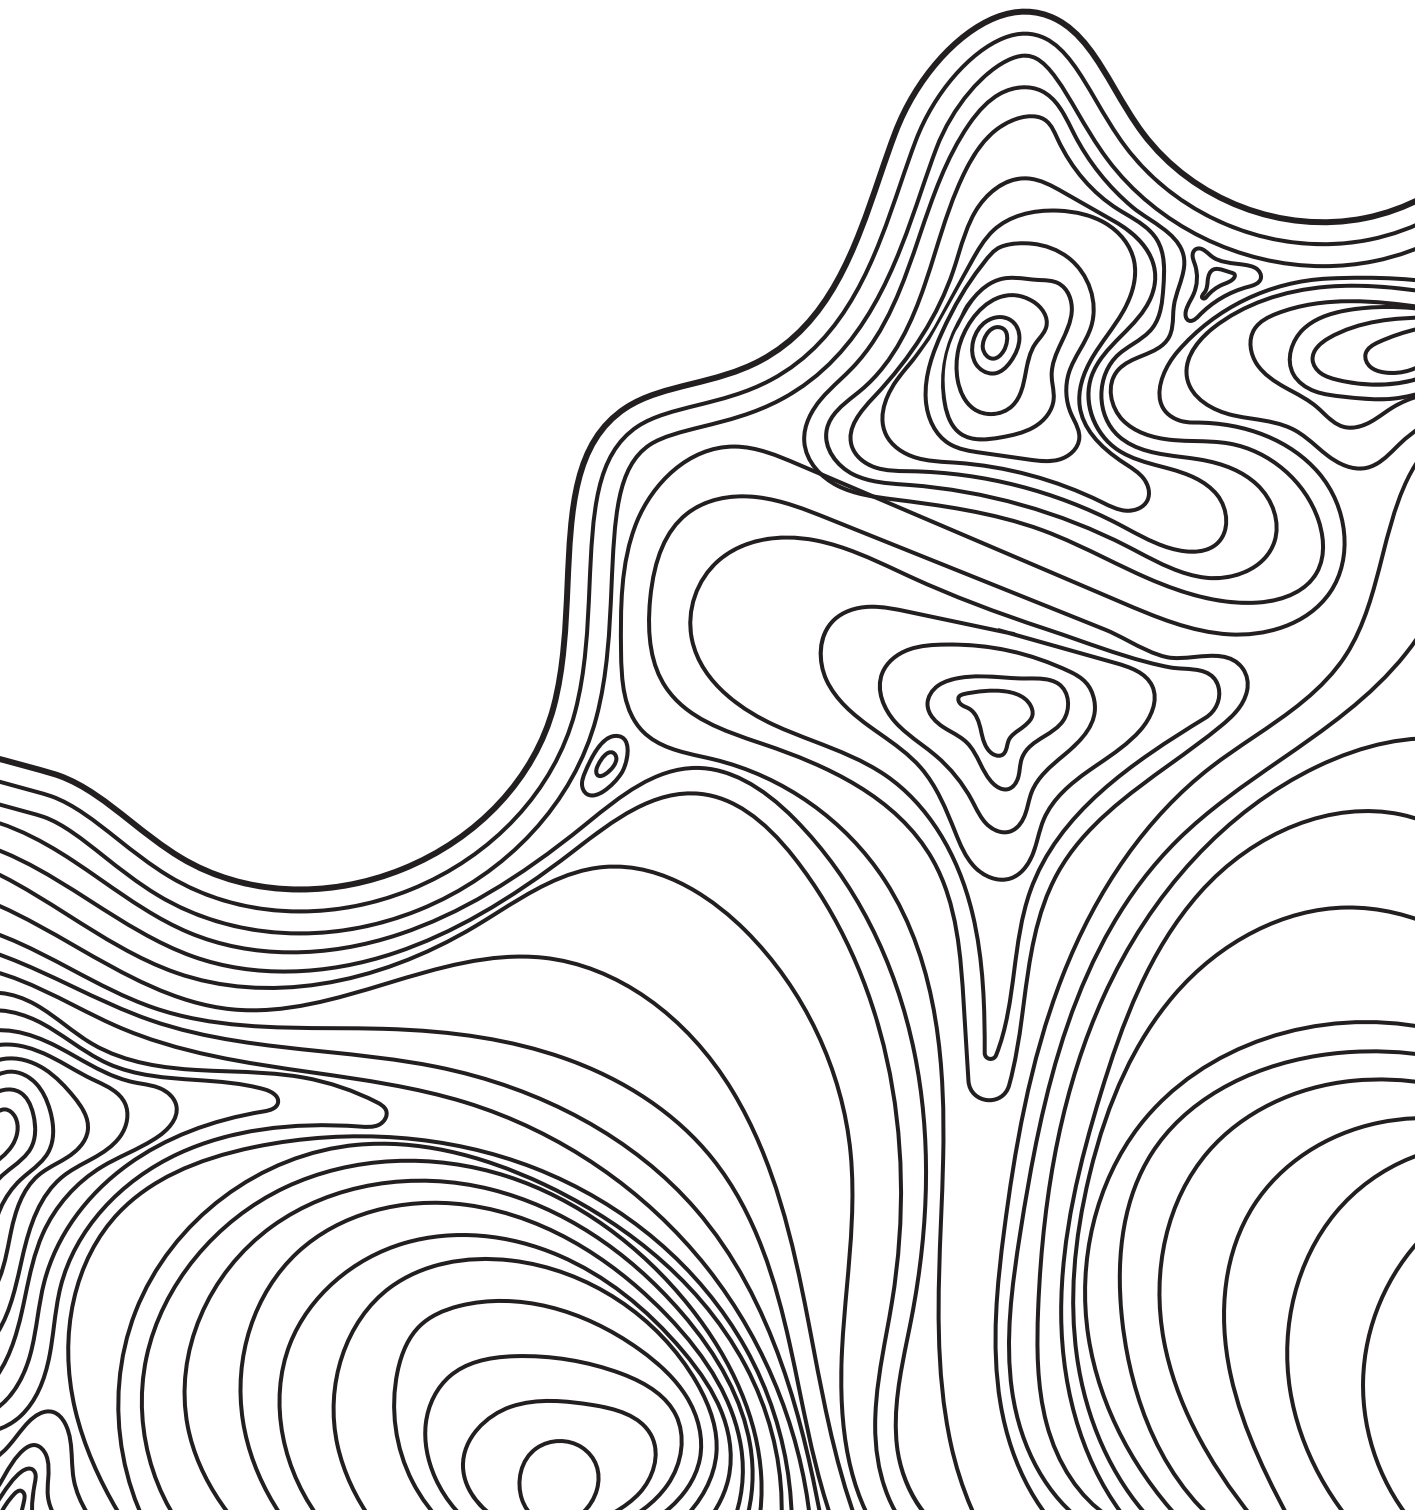
[picture p214: page 1]
