oserratr/head-md-caran-ache-project/process/2023-11-27 a 2023-11-29/tests-arduino/sketch_nov29d/sketch_nov29d.ino

#include <Servo.h>

Servo servo;
int angle = 10;

void setup() {
  servo.attach(8);
  servo.write(angle);
}


void loop() 
{ 
 // scan from 0 to 180 degrees
  for(angle = 10; angle < 180; angle++)  
  {                                  
    servo.write(angle);               
    delay(15);                   
  } 
  // now scan back from 180 to 0 degrees
  for(angle = 180; angle > 10; angle--)    
  {                                
    servo.write(angle);           
    delay(15);       
  } 
}
